cheshire-smile/CSULA_ECST_Claw_Machine/Design_Files/Alice - Claw_Machine_V3/7_3 Cube Parts/m5-hex-socket-screw/Renderings/M5x6.JPG

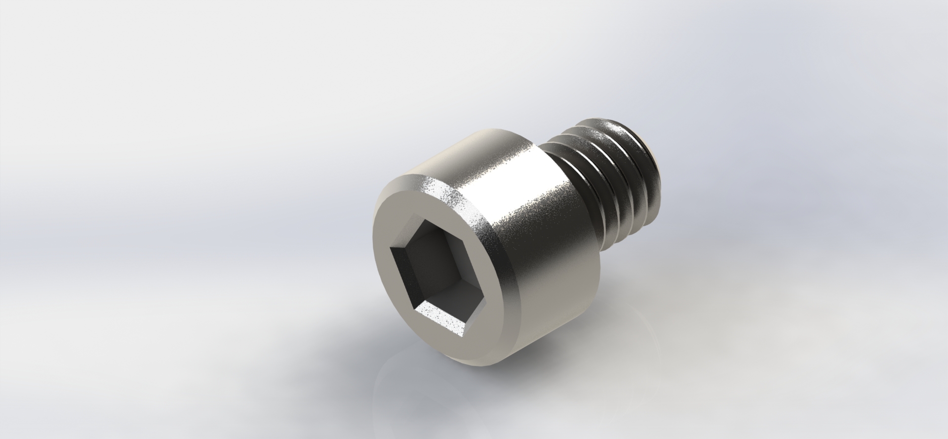
Design_Files/Alice - Claw_Machine_V3/7_3 Cube Parts/m5-hex-socket-screw/Renderings/M5x6.JPG
