cheshire-smile/CSULA_ECST_Claw_Machine/Design_Files/Alice - Claw_Machine_V3/7_3 Cube Parts/acyrlic/25.5inx22.44insideacyrlic.SLDPRT

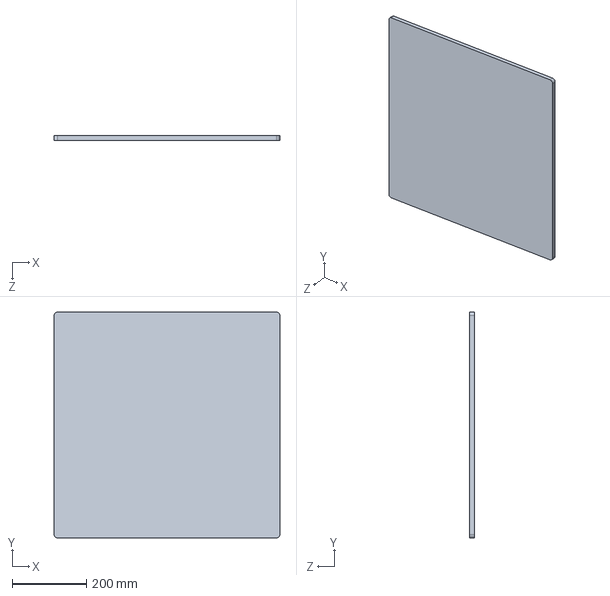
[picture p12: CAD file, 2025-05-13]
Design_Files/Alice - Claw_Machine_V3/7_3 Cube Parts/acyrlic/25.5inx22.44insideacyrlic.SLDPRT
609.6 x 609.6 x 12.7 mm
