cheshire-smile/CSULA_ECST_Claw_Machine/Design_Files/Alice - Claw_Machine_V3/7_3 Cube Parts/Sanwa JLF-TP-8YT  16Gate.step

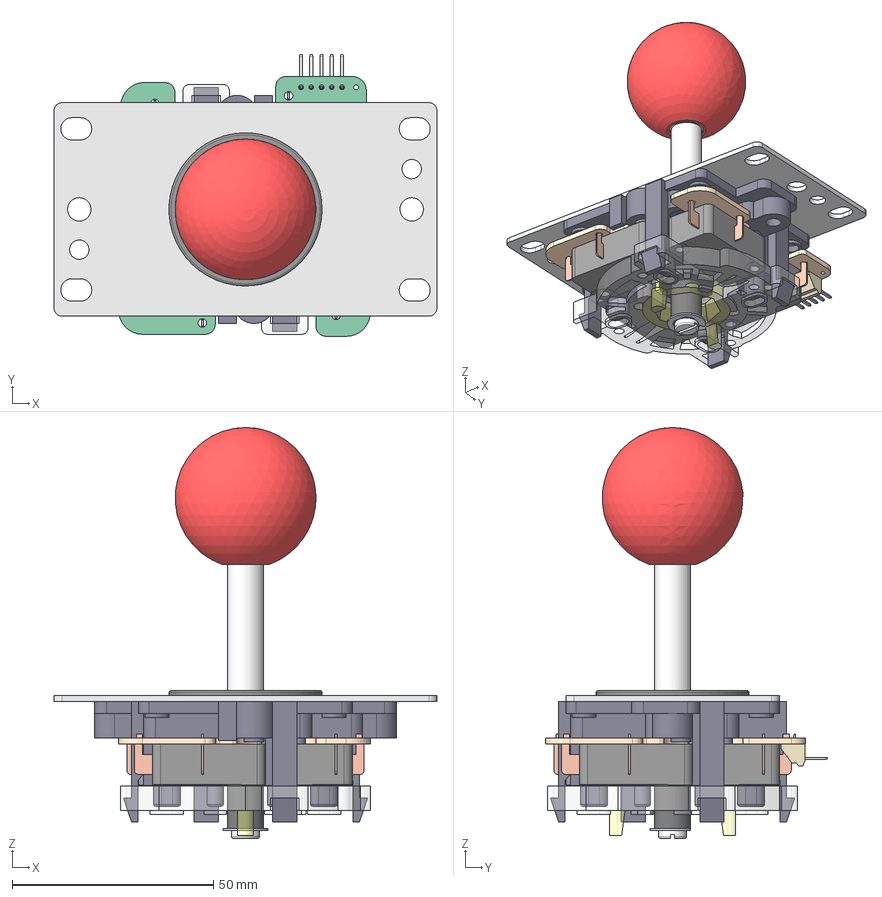
[picture p14: CAD file, 2025-05-13]
Design_Files/Alice - Claw_Machine_V3/7_3 Cube Parts/joystick and button/Sanwa JLF-TP-8YT 16Gate.step
95.0 x 69.9 x 102.0 mm
Connector 5P
JLF-P1 Mounting Plate
Sanwa LB-35 Balltop Dark Red
Sanwa JL-S9F Shaft
Solo Sanwa JLF Dustwasher
Sanwa LB-30 N-S Battop Adapter
Sanwa JLF P-2 Main Body
Sanwa JLF-P-4 Pivot
Push Button Arcade
Push Button Arcade_clne150
Push Button Arcade_clne151
Push Button Arcade_clne152
Sanwa JLF Actuator
Circlip
Sanwa JLF-P-6 Pressure Spring Base
Sanwa TP-MA PCB
Sanwa JLF-MW Washer
Sanwa JLF Spring
Sanwa GT-8F 16-Way Restrictor Plate
M3x10-Screw
M3x10-Screw001
M3x10-Screw002
M3x10-Screw003
M3-Nut
M3-Nut004
M3-Nut007
M3-Nut006
Sanwa GT Restrictor Plate
