cheshire-smile/CSULA_ECST_Claw_Machine/Design_Files/Alice - Claw_Machine_V3/7_3 Cube Parts/Microprocessor Cover.SLDPRT

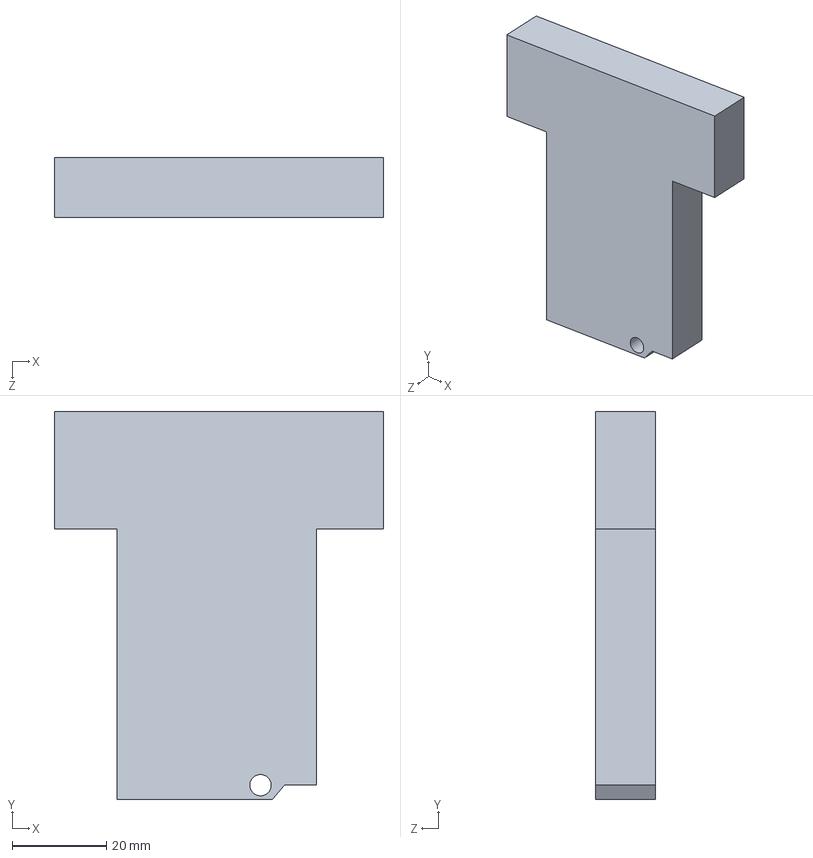
[picture p15: CAD file, 2025-05-13]
Design_Files/Alice - Claw_Machine_V3/7_3 Cube Parts/Microprocessor Cover.SLDPRT
70.0 x 82.5 x 12.7 mm
