cheshire-smile/CSULA_ECST_Claw_Machine/Design_Files/Alice - Claw_Machine_V3/7_3 Cube Parts/Sub_Assemblys/Corner_Idler_Pulley/Idler__Pulley/Bearing Seal, GT2 Timing Idler Pulley, Configurable.SLDPRT

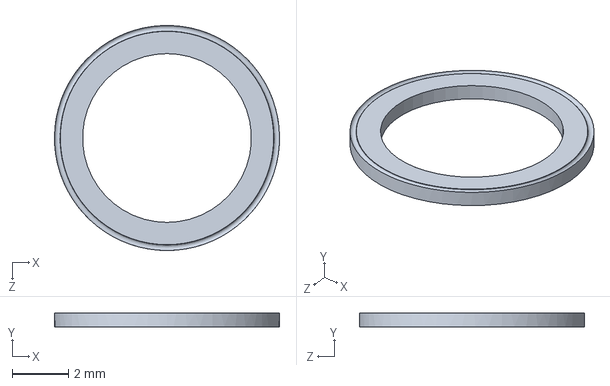
[picture p16: CAD file, 2025-05-13]
Design_Files/Alice - Claw_Machine_V3/7_3 Cube Parts/Sub_Assemblys/Corner_Idler_Pulley/Idler__Pulley/Bearing Seal, GT2 Timing Idler Pulley, Configurable.SLDPRT
8.00 x 0.5 x 8.00 mm
