cheshire-smile/CSULA_ECST_Claw_Machine/Design_Files/Alice - Claw_Machine_V3/7_3 Cube Parts/Sub_Assemblys/dc-micro-metal-gearmotor/Motor.stp

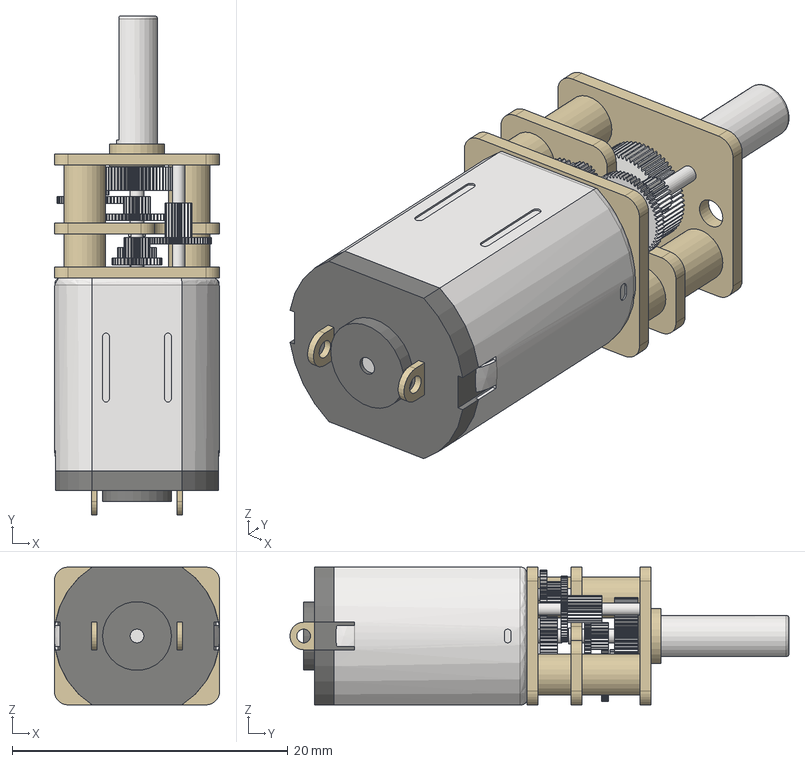
[picture p17: CAD file, 2025-05-13]
Design_Files/Alice - Claw_Machine_V3/7_3 Cube Parts/Sub_Assemblys/dc-micro-metal-gearmotor/Motor.stp
12.0 x 36.2 x 10.0 mm
Base
Rotor
Apoio Contato
Contato
Suporte Contato
Imãs
Terminais x 2
Escovas
Chapa Inferior
Chapa Intermediária
Chapa Superior
Eixo Maior - Engrenagem
Eixo Menor - Engrenagem
Parafuso x 2
Suporte Bobinas
Eixo Menor - Engrenagem_1
Engrenagem reta1
Engrenagem reta2
Engrenagem reta1_1
Engrenagem reta2_1
Eixo - Encaixe D
Engrenagem reta1_2
Engrenagem reta2_2
Engrenagem reta1_3
Engrenagem reta2_3
Engrenagem reta1_4
Engrenagem reta2_4
Carcaça
