cheshire-smile/CSULA_ECST_Claw_Machine/Design_Files/Alice - Claw_Machine_V3/7_3 Cube Parts/Sub_Assemblys/nema-17-stepper-motor/NEMA 17 Stepper Motor Shaft.SLDPRT

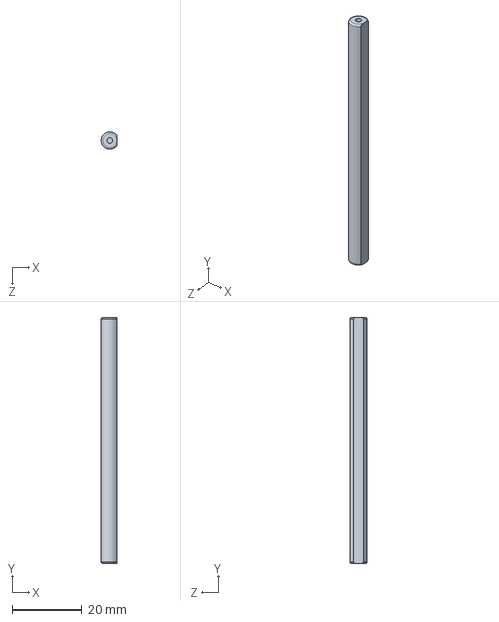
[picture p18: CAD file, 2025-05-13]
Design_Files/Alice - Claw_Machine_V3/7_3 Cube Parts/Sub_Assemblys/nema-17-stepper-motor/NEMA 17 Stepper Motor Shaft.SLDPRT
4.50 x 70.3 x 5.00 mm
