cheshire-smile/CSULA_ECST_Claw_Machine/Design_Files/Alice - Claw_Machine_V3/7_3 Cube Parts/Sub_Assemblys/V-Slot_Gantry_Plate/V-Slot Gantry Kit - 20mm.step

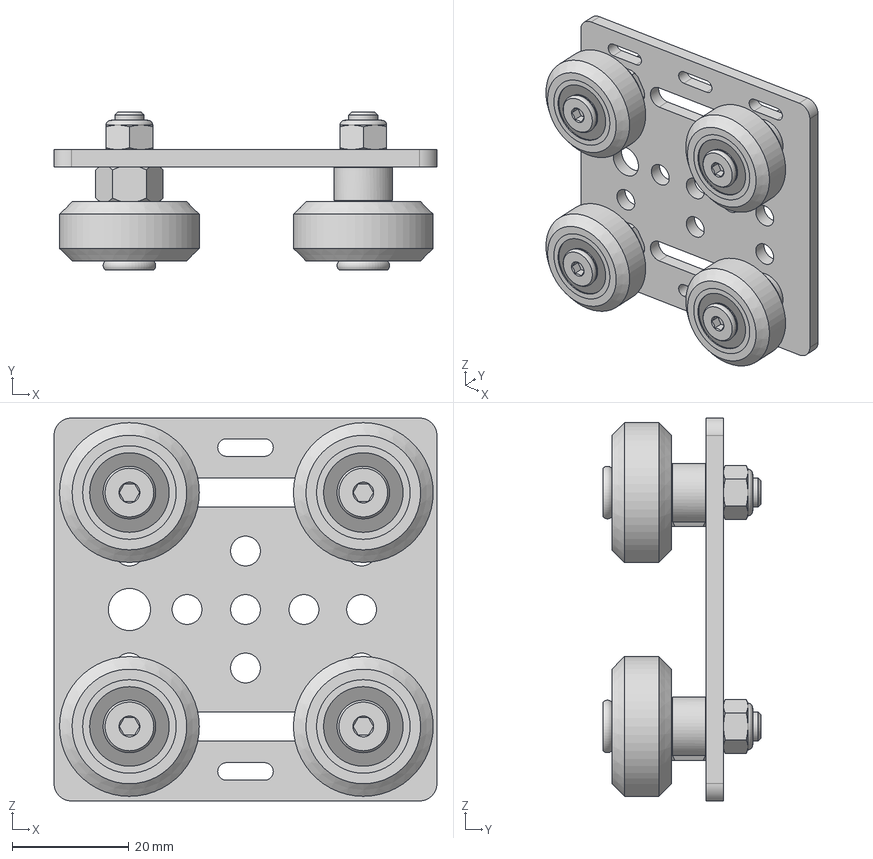
[picture p19: CAD file, 2025-05-13]
Design_Files/Alice - Claw_Machine_V3/7_3 Cube Parts/Sub_Assemblys/V-Slot_Gantry_Plate/V-Slot Gantry Kit - 20mm.step
65.5 x 27.0 x 65.5 mm
V-Slot Gantry Plate 20mm
Low Profile Screw M5 v1 x 4
Nylon Insert Lock Nut M5 x 4
Aluminum Spacer 6mm x 2
Eccentric Spacer 6mm v1 x 2
Ball Bearing 5 x 16 x 5 x 8
Precision Shim 8 x 5 x 1 x 4
Xtreme Solid V Wheel x 4
