cheshire-smile/CSULA_ECST_Claw_Machine/Design_Files/Alice - Claw_Machine_V3/7_3 Cube Parts/Winch/Updated Spool.SLDPRT

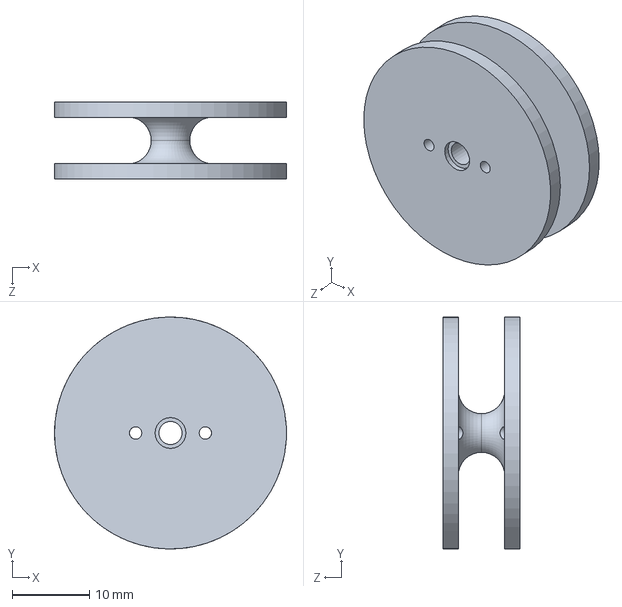
[picture p20: CAD file, 2025-05-13]
Design_Files/Alice - Claw_Machine_V3/7_3 Cube Parts/Winch/Updated Spool.SLDPRT
30.0 x 30.0 x 10.0 mm
