cheshire-smile/CSULA_ECST_Claw_Machine/Design_Files/Alice - Claw_Machine_V3/7_3 Cube Parts/wood/25.5inx13.57infrontbottomwoodhole.SLDPRT

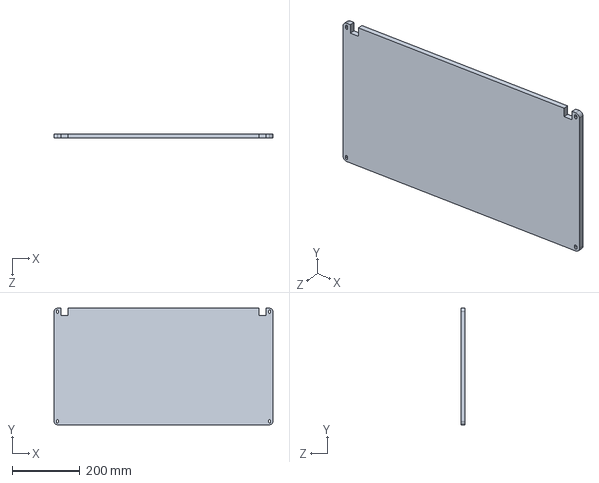
[picture p21: CAD file, 2025-05-13]
Design_Files/Alice - Claw_Machine_V3/7_3 Cube Parts/wood/25.5inx13.57infrontbottomwoodhole.SLDPRT
647.7 x 344.7 x 12.7 mm
