cheshire-smile/CSULA_ECST_Claw_Machine/Design_Files/Alice - Claw_Machine_V3/ST-M11.SLDPRT

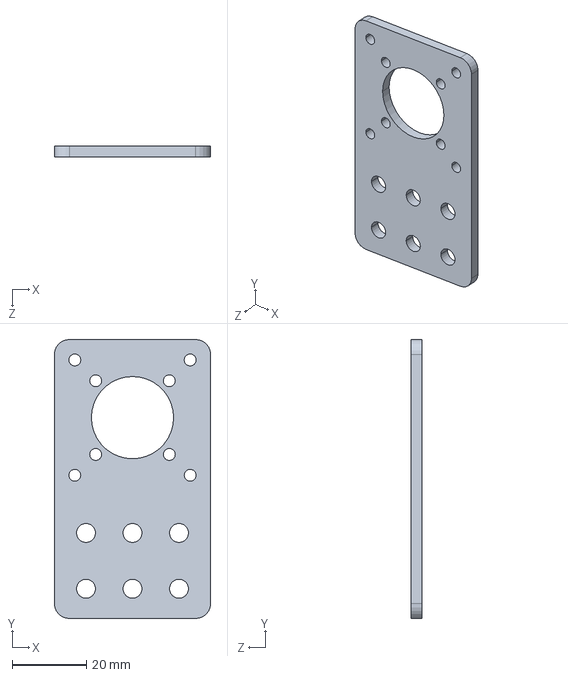
[picture p22: CAD file, 2025-05-13]
Design_Files/Alice - Claw_Machine_V3/ST-M11.SLDPRT
42.0 x 75.0 x 3.00 mm
