cheshire-smile/CSULA_ECST_Claw_Machine/Design_Files/Claw_Machine_V5/7_3 Cube Parts/acyrlic/25.5inx22.35infrontacyrlic.SLDPRT

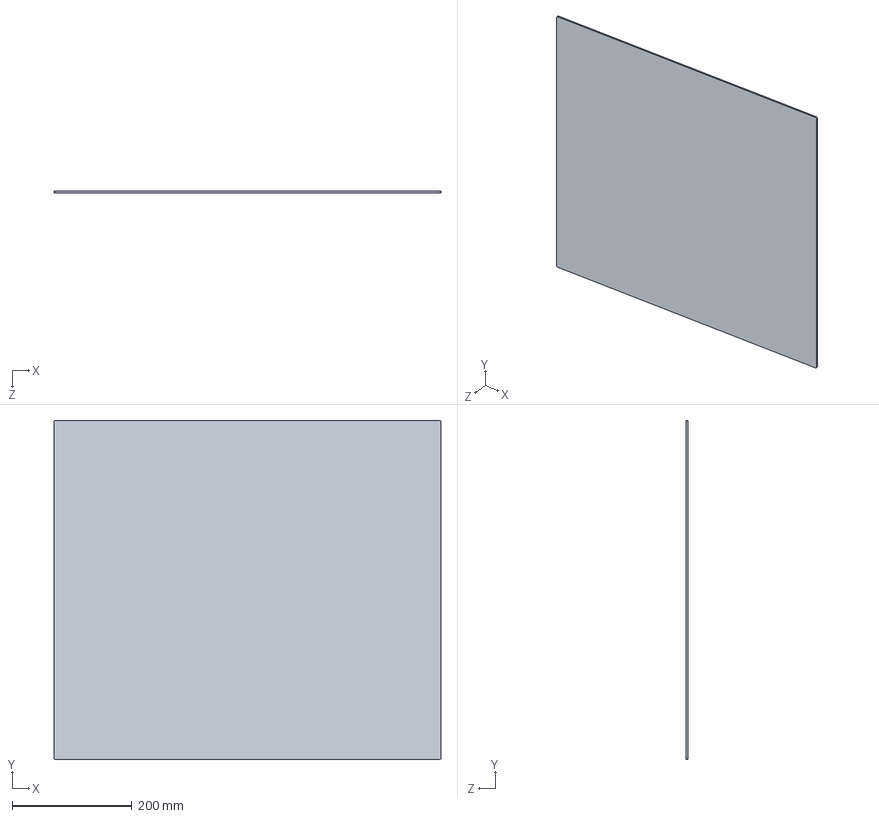
[picture p23: CAD file, 2025-09-01]
Design_Files/Claw_Machine_V5/7_3 Cube Parts/acyrlic/25.5inx22.35infrontacyrlic.SLDPRT
647.7 x 567.7 x 3.17 mm
