cheshire-smile/CSULA_ECST_Claw_Machine/Design_Files/Claw_Machine_V5/7_3 Cube Parts/aluminum_extrusion_2020/30inaluminum.SLDPRT

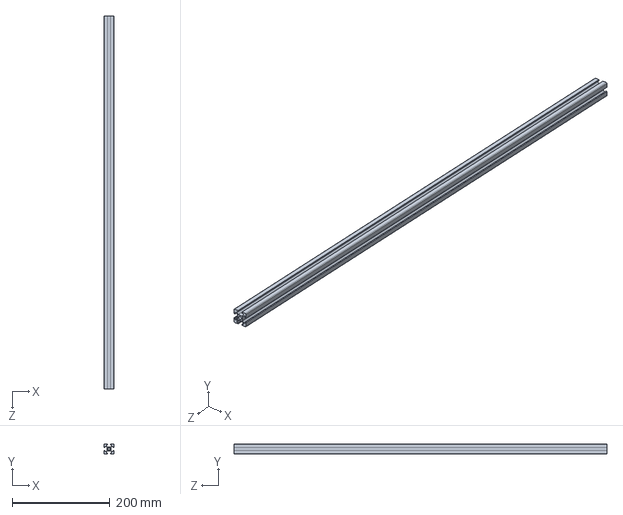
[picture p24: CAD file, 2025-09-01]
Design_Files/Claw_Machine_V5/7_3 Cube Parts/aluminum_extrusion_2020/30inaluminum.SLDPRT
20.0 x 20.0 x 762.0 mm
