cheshire-smile/CSULA_ECST_Claw_Machine/Design_Files/Claw_Machine_V5/7_3 Cube Parts/Sub_Assemblys/2020-extrusion-gt2-belt-tensioner/2020 Tensioner Long side.SLDPRT

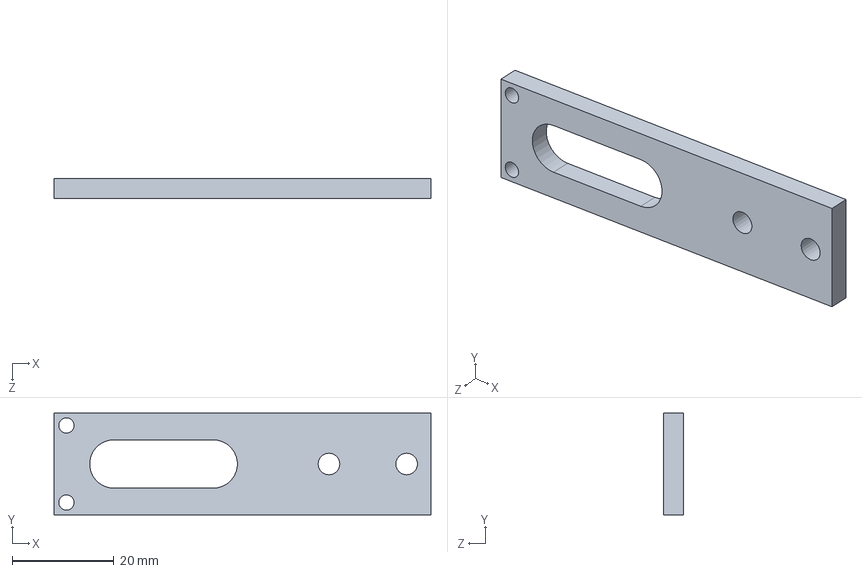
[picture p25: CAD file, 2025-09-01]
Design_Files/Claw_Machine_V5/7_3 Cube Parts/Sub_Assemblys/2020-extrusion-gt2-belt-tensioner/2020 Tensioner Long side.SLDPRT
74.0 x 20.0 x 4.00 mm
