cheshire-smile/CSULA_ECST_Claw_Machine/Design_Files/Claw_Machine_V5/7_3 Cube Parts/Sub_Assemblys/Corner_Idler_Pulley/Idler__Pulley/Bearing Ball, GT2 Timing Idler Pulley, Configurable.SLDPRT

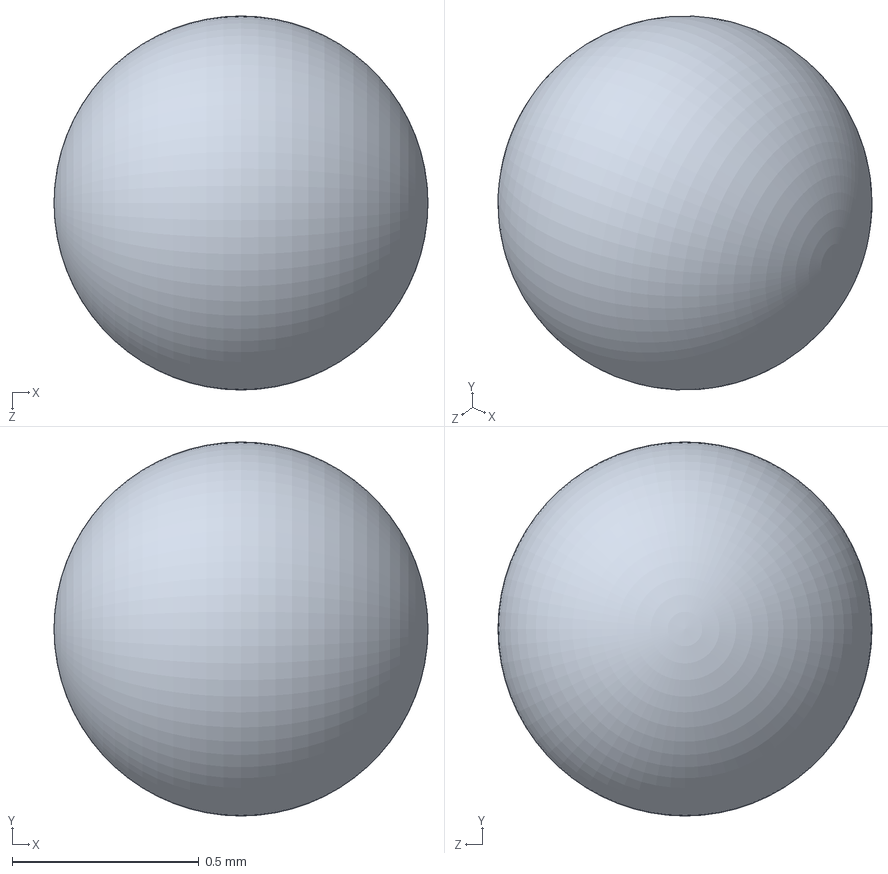
[picture p26: CAD file, 2025-09-01]
Design_Files/Claw_Machine_V5/7_3 Cube Parts/Sub_Assemblys/Corner_Idler_Pulley/Idler__Pulley/Bearing Ball, GT2 Timing Idler Pulley, Configurable.SLDPRT
1.00 x 1.00 x 1.00 mm
