cheshire-smile/CSULA_ECST_Claw_Machine/Design_Files/Claw_Machine_V5/7_3 Cube Parts/Sub_Assemblys/Winch/Gantry_Plate.SLDPRT

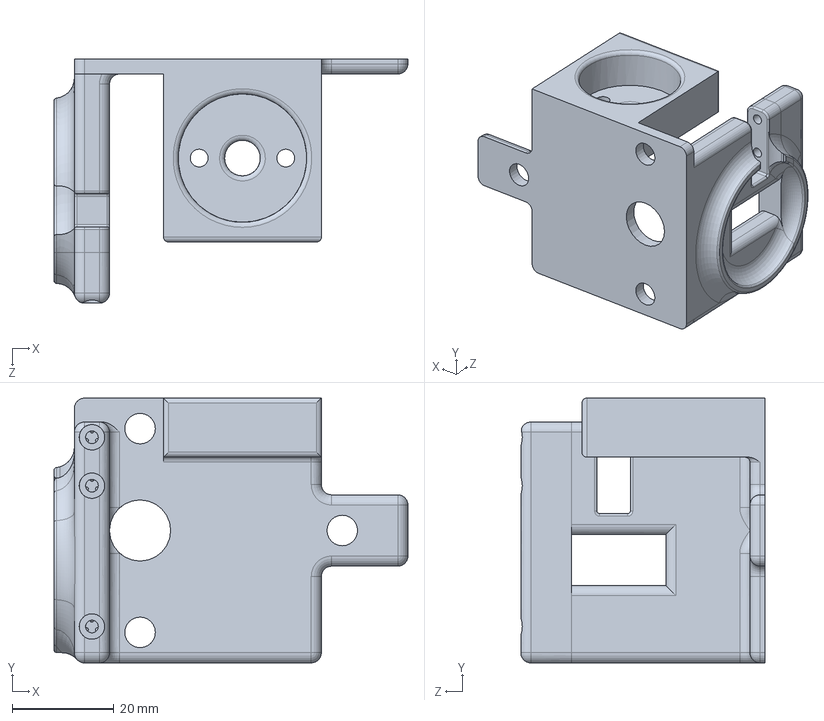
[picture p27: CAD file, 2025-09-02]
Design_Files/Claw_Machine_V5/7_3 Cube Parts/Sub_Assemblys/Winch/Gantry_Plate.SLDPRT
69.5 x 52.0 x 48.0 mm
