cheshire-smile/CSULA_ECST_Claw_Machine/Design_Files/Claw_Machine_V5/7_3 Cube Parts/wood/23.92inx4.43infrontwoodforjoystick.SLDPRT

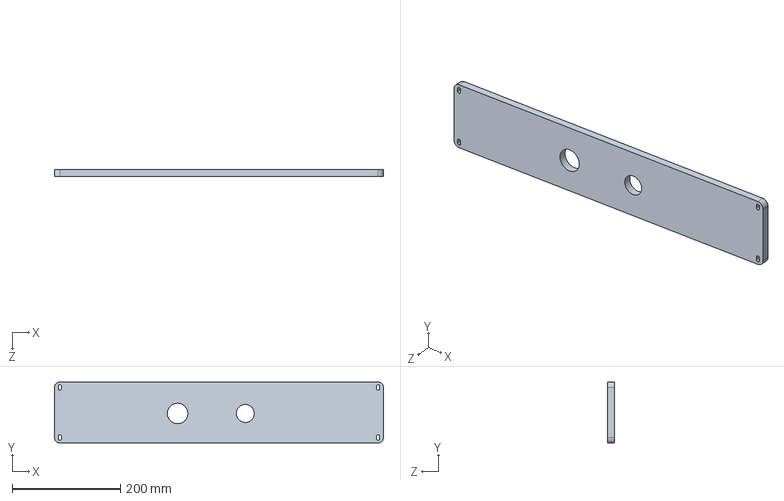
[picture p28: CAD file, 2025-09-01]
Design_Files/Claw_Machine_V5/7_3 Cube Parts/wood/23.92inx4.43infrontwoodforjoystick.SLDPRT
607.6 x 112.5 x 12.7 mm
