cheshire-smile/CSULA_ECST_Claw_Machine/Design_Files/Claw_Machine_V5/7_3 Cube Parts/X-Axis_Mounting_Bracket.SLDPRT

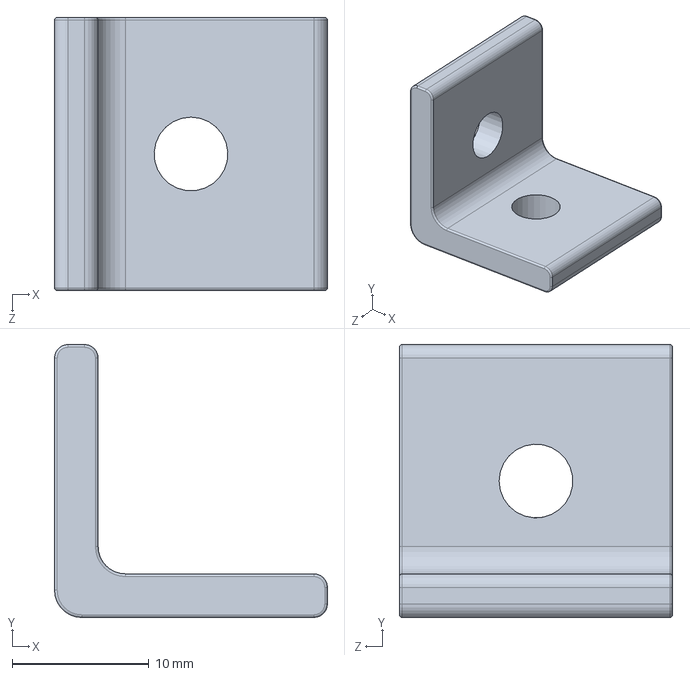
[picture p29: CAD file, 2025-09-01]
Design_Files/Claw_Machine_V5/7_3 Cube Parts/X-Axis_Mounting_Bracket.SLDPRT
20.0 x 20.0 x 20.0 mm
