cheshire-smile/CSULA_ECST_Claw_Machine/Design_Files/Alice - Claw_Machine_V3/7_3 Cube Parts/aluminum_extrusion_2020/36inaluminum.SLDPRT

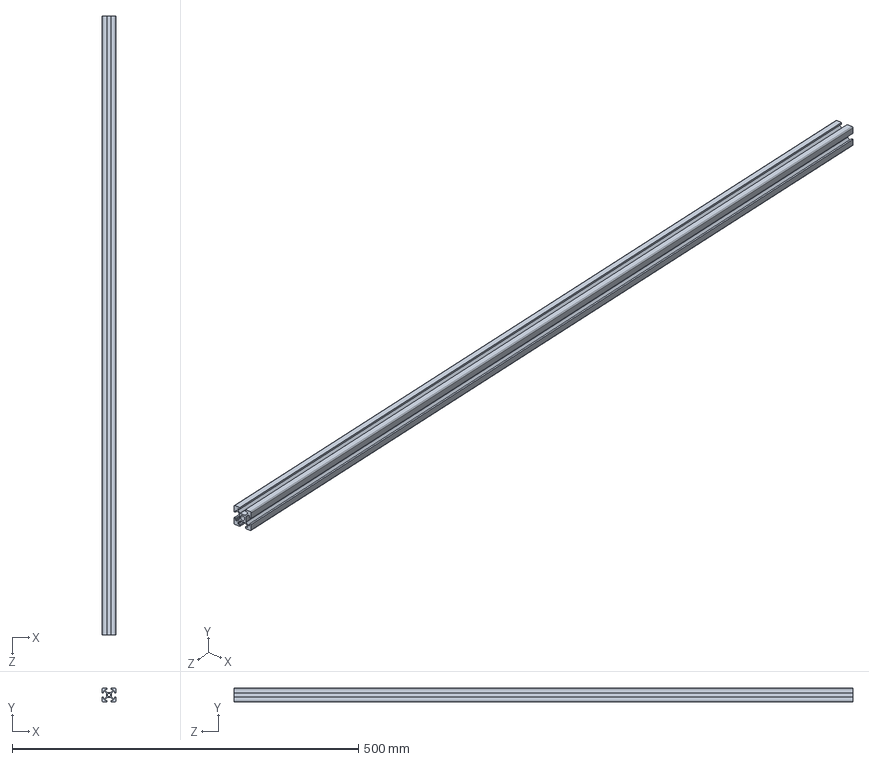
[picture p30: CAD file, 2025-05-13]
Design_Files/Alice - Claw_Machine_V3/7_3 Cube Parts/aluminum_extrusion_2020/36inaluminum.SLDPRT
20.0 x 20.0 x 894.4 mm
