cheshire-smile/CSULA_ECST_Claw_Machine/Design_Files/Alice - Claw_Machine_V3/7_3 Cube Parts/joystick and button/Adafruit 30mm Button with LED v2.step

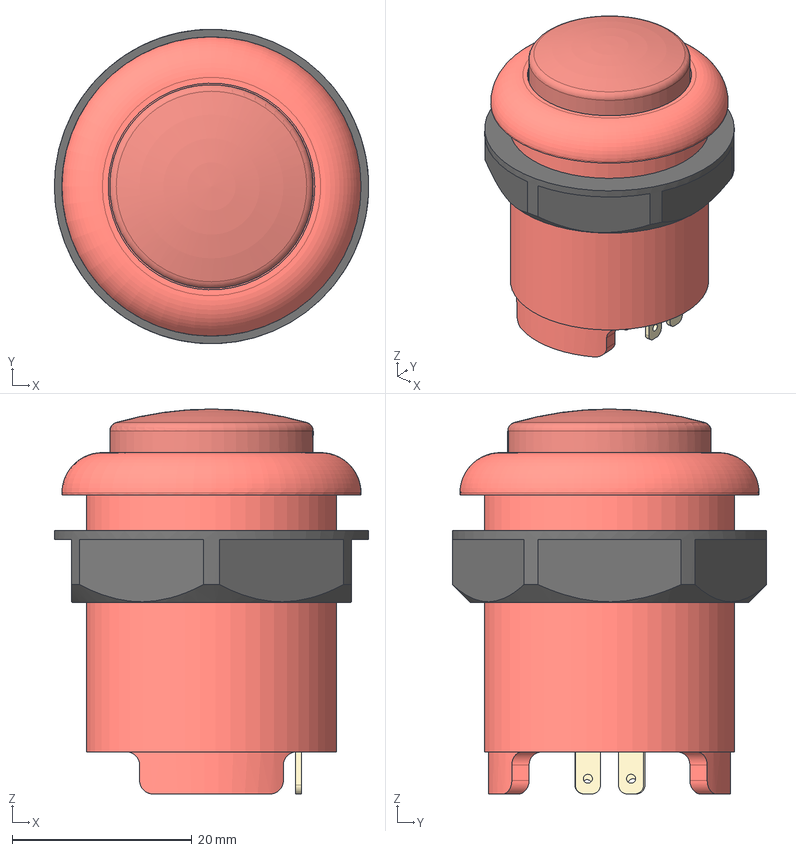
[picture p31: CAD file, 2025-05-13]
Design_Files/Alice - Claw_Machine_V3/7_3 Cube Parts/joystick and button/Adafruit 30mm Button with LED v2.step
35.0 x 35.0 x 42.9 mm
shell_body
nut
button_body
pins
led_pins
