cheshire-smile/CSULA_ECST_Claw_Machine/Design_Files/Alice - Claw_Machine_V3/7_3 Cube Parts/Pulley_GT2_20T_b5.SLDPRT

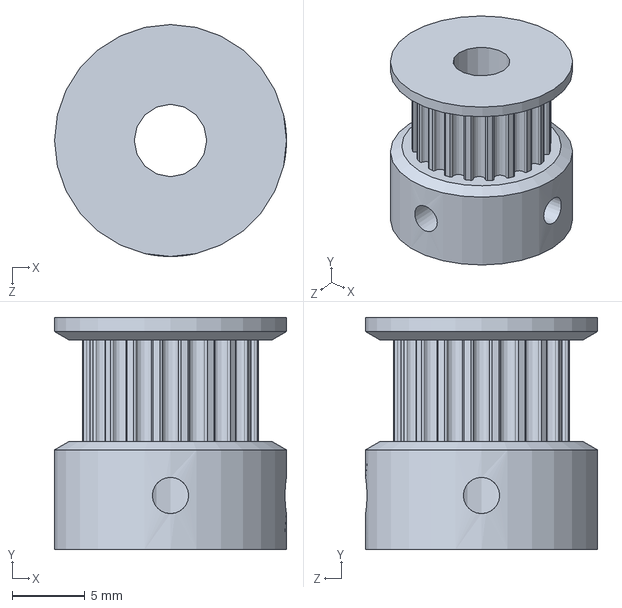
[picture p32: CAD file, 2025-05-13]
Design_Files/Alice - Claw_Machine_V3/7_3 Cube Parts/Pulley_GT2_20T_b5.SLDPRT
16.0 x 16.0 x 16.0 mm
