cheshire-smile/CSULA_ECST_Claw_Machine/Design_Files/Alice - Claw_Machine_V3/7_3 Cube Parts/Sub_Assemblys/2020-extrusion-gt2-belt-tensioner/2020 Belt Tensioner G_K.STEP

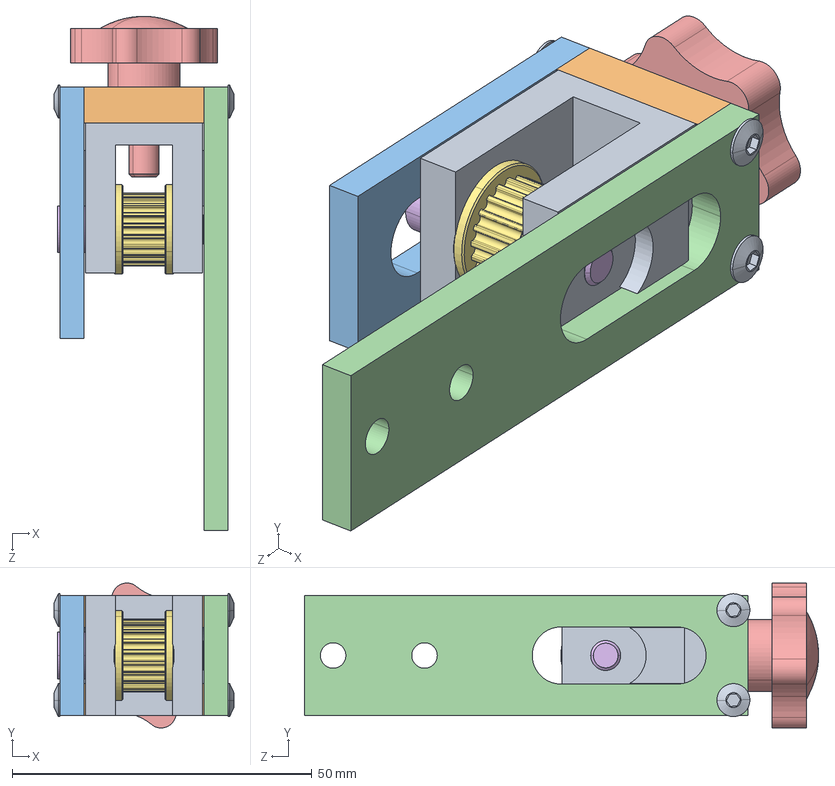
[picture p33: CAD file, 2025-05-13]
Design_Files/Alice - Claw_Machine_V3/7_3 Cube Parts/Sub_Assemblys/2020-extrusion-gt2-belt-tensioner/2020 Belt Tensioner G_K.STEP
30.0 x 24.2 x 85.8 mm
2020 Tensioner Pulley Cradle
2020 Tensioner Rear
2020 Tensioner Short side
2020 Tensioner Long side
2020 Tensioner Adjusting Screw
M5 Cap head Screw
GT2_Idler_20T.step
Ball bearing (5x9x3)mm003.step
Ball bearing (5x9x3)mm004.step
M3x10mm bolt x 4
