cheshire-smile/CSULA_ECST_Claw_Machine/Design_Files/Alice - Claw_Machine_V3/7_3 Cube Parts/Sub_Assemblys/Corner_Idler_Pulley/Idler__Pulley/Bearing Inner Ring, GT2 Timing Idler Pulley, Configurable.SLDPRT

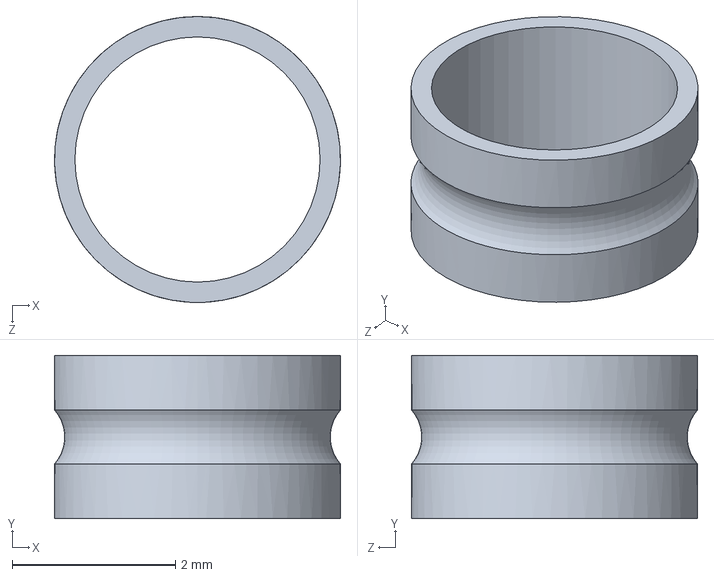
[picture p34: CAD file, 2025-05-13]
Design_Files/Alice - Claw_Machine_V3/7_3 Cube Parts/Sub_Assemblys/Corner_Idler_Pulley/Idler__Pulley/Bearing Inner Ring, GT2 Timing Idler Pulley, Configurable.SLDPRT
3.50 x 2.00 x 3.50 mm
