cheshire-smile/CSULA_ECST_Claw_Machine/Design_Files/Alice - Claw_Machine_V3/7_3 Cube Parts/Sub_Assemblys/nema-17-stepper-motor/NEMA 17 Stepper Motor SIMPLE.IGS

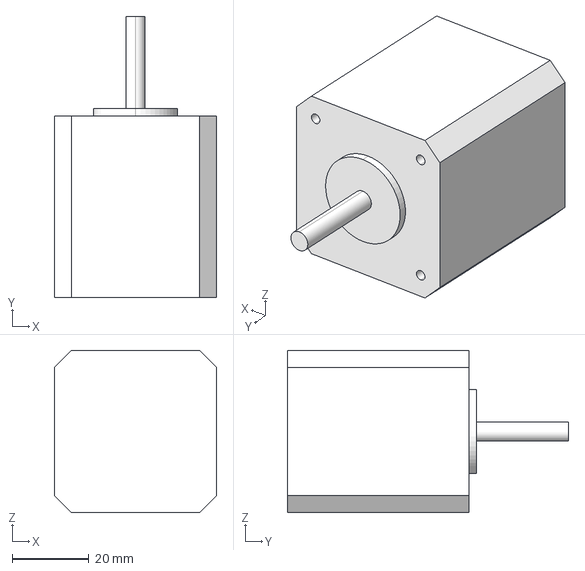
[picture p35: CAD file, 2025-05-13]
Design_Files/Alice - Claw_Machine_V3/7_3 Cube Parts/Sub_Assemblys/nema-17-stepper-motor/NEMA 17 Stepper Motor SIMPLE.IGS
42.3 x 73.3 x 42.3 mm
