cheshire-smile/CSULA_ECST_Claw_Machine/Design_Files/Alice - Claw_Machine_V3/7_3 Cube Parts/Winch/Outer part 26mm.SLDPRT

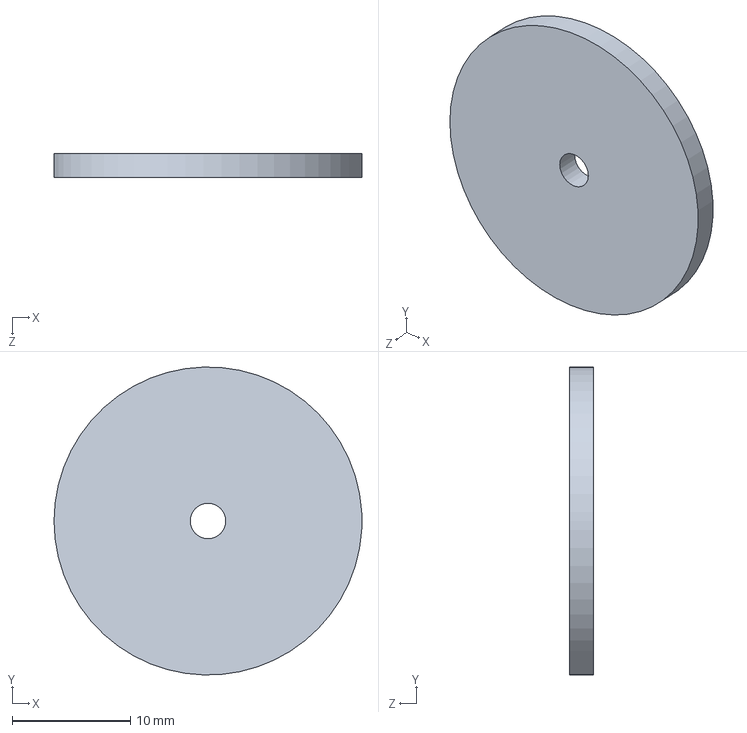
[picture p36: CAD file, 2025-05-13]
Design_Files/Alice - Claw_Machine_V3/7_3 Cube Parts/Winch/Outer part 26mm.SLDPRT
26.0 x 26.0 x 2.00 mm
