cheshire-smile/CSULA_ECST_Claw_Machine/Design_Files/Claw_Machine_V5/7_3 Cube Parts/acyrlic/25.5inx22.44insideacyrlic.SLDPRT

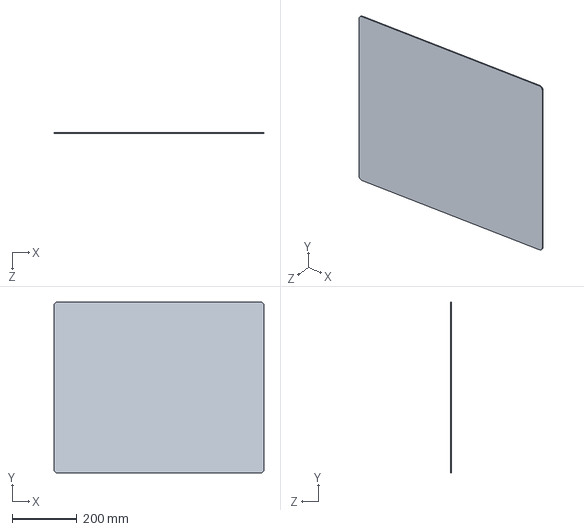
[picture p37: CAD file, 2025-09-01]
Design_Files/Claw_Machine_V5/7_3 Cube Parts/acyrlic/25.5inx22.44insideacyrlic.SLDPRT
647.7 x 527.0 x 3.17 mm
