cheshire-smile/CSULA_ECST_Claw_Machine/Design_Files/Claw_Machine_V5/7_3 Cube Parts/Sub_Assemblys/Mini Servo operated Claw Machine Claw Grabber - 4826548/files/Claw_cover.SLDPRT

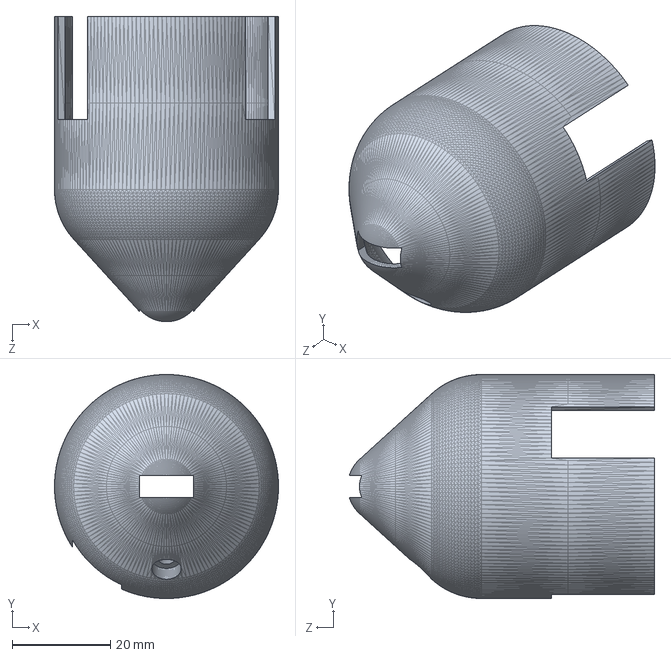
[picture p40: CAD file, 2025-09-01]
Design_Files/Claw_Machine_V5/7_3 Cube Parts/Sub_Assemblys/Mini Servo operated Claw Machine Claw Grabber - 4826548/files/Claw_cover.SLDPRT
45.5 x 45.5 x 62.0 mm
