cheshire-smile/CSULA_ECST_Claw_Machine/Design_Files/Claw_Machine_V5/7_3 Cube Parts/Sub_Assemblys/nema-17-stepper-motor/NEMA 17 Stepper Motor Top.SLDPRT

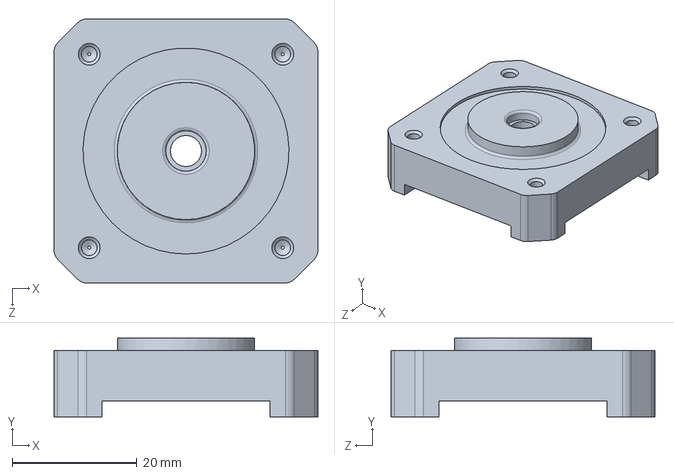
[picture p41: CAD file, 2025-09-01]
Design_Files/Claw_Machine_V5/7_3 Cube Parts/Sub_Assemblys/nema-17-stepper-motor/NEMA 17 Stepper Motor Top.SLDPRT
42.3 x 12.6 x 42.3 mm
