cheshire-smile/CSULA_ECST_Claw_Machine/Design_Files/Claw_Machine_V5/7_3 Cube Parts/Sub_Assemblys/Winch/Crane_Spool_forCNC.SLDPRT

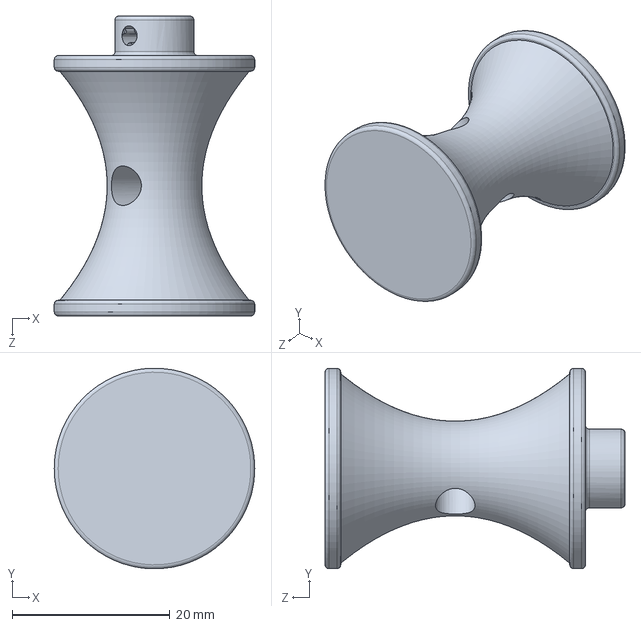
[picture p42: CAD file, 2025-09-02]
Design_Files/Claw_Machine_V5/7_3 Cube Parts/Sub_Assemblys/Winch/Crane_Spool_forCNC.SLDPRT
25.4 x 25.4 x 38.0 mm
