cheshire-smile/CSULA_ECST_Claw_Machine/Design_Files/Alice - Claw_Machine_V3/7_3 Cube Parts/wood/24.08inx23.92ininsidewood.SLDPRT

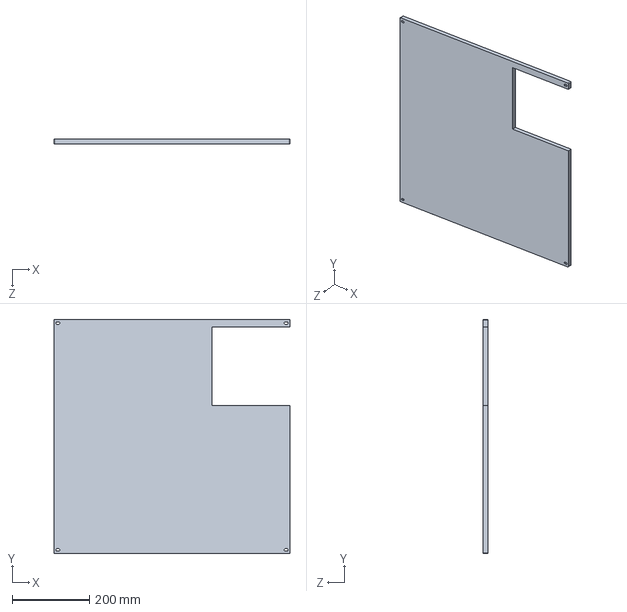
[picture p43: CAD file, 2025-05-13]
Design_Files/Alice - Claw_Machine_V3/7_3 Cube Parts/wood/24.08inx23.92ininsidewood.SLDPRT
611.6 x 607.6 x 12.7 mm
