cheshire-smile/CSULA_ECST_Claw_Machine/Design_Files/Claw_Machine_V5/7_3 Cube Parts/acyrlic/25.5inx22.35infrontacyrlic87.DXF

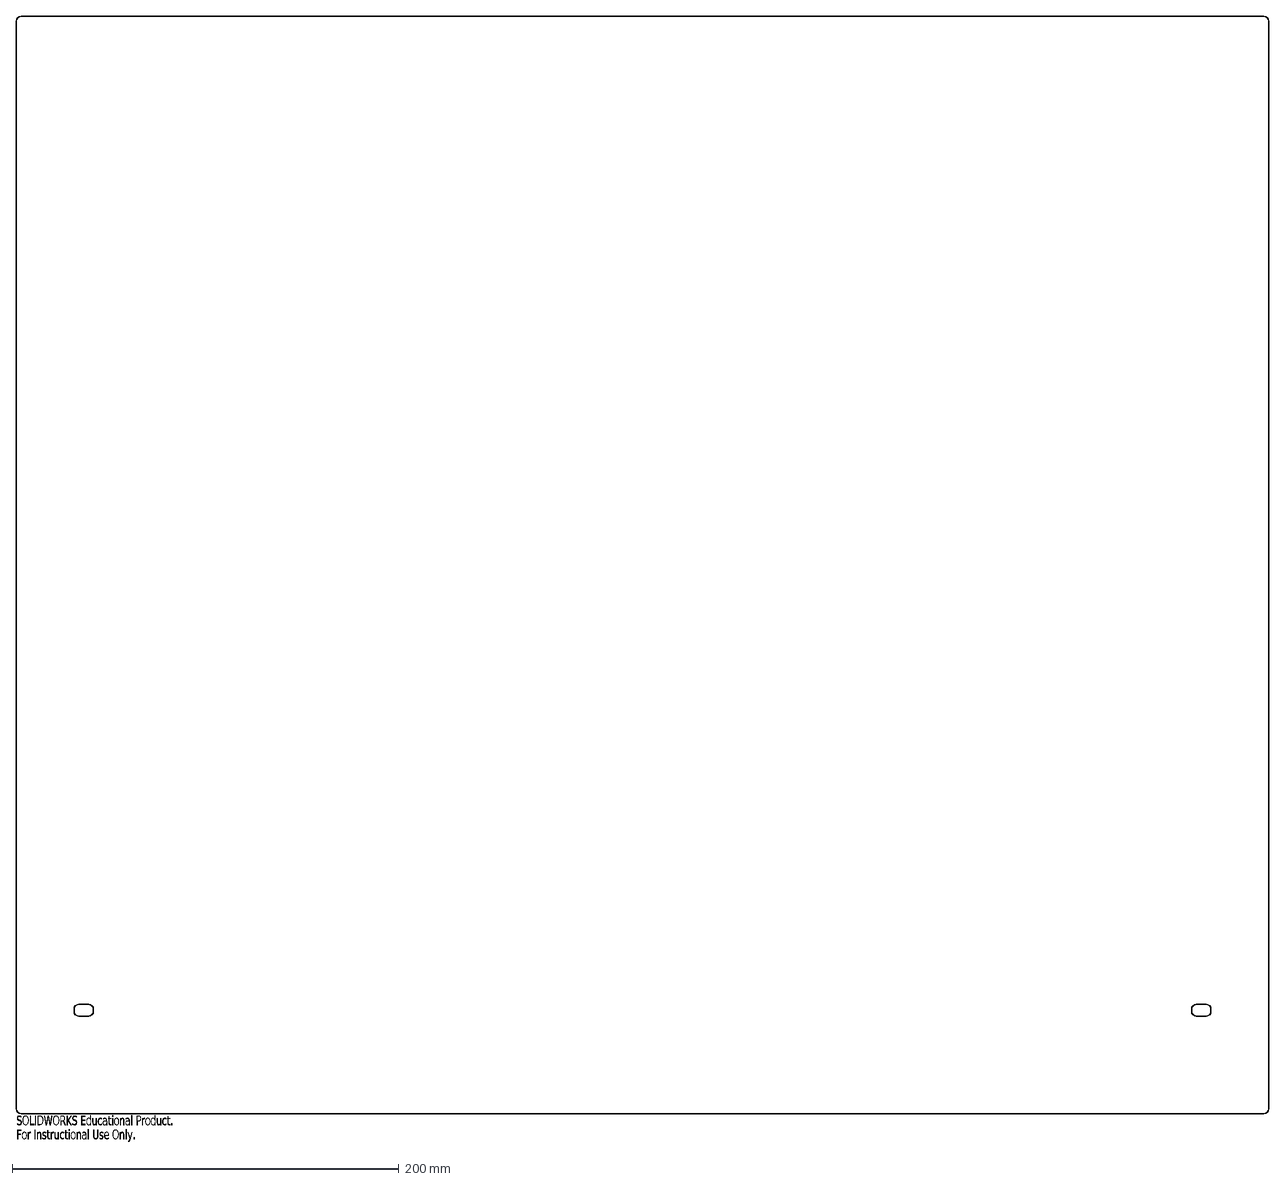
[picture p44: CAD file, 2025-05-13]
Design_Files/Claw_Machine_V5/7_3 Cube Parts/acyrlic/25.5inx22.35infrontacyrlic87.DXF
SOLIDWORKS Educational Product.
For Instructional Use Only.
