cheshire-smile/CSULA_ECST_Claw_Machine/Design_Files/Claw_Machine_V5/7_3 Cube Parts/Corner_Idler_Pulley.SLDPRT

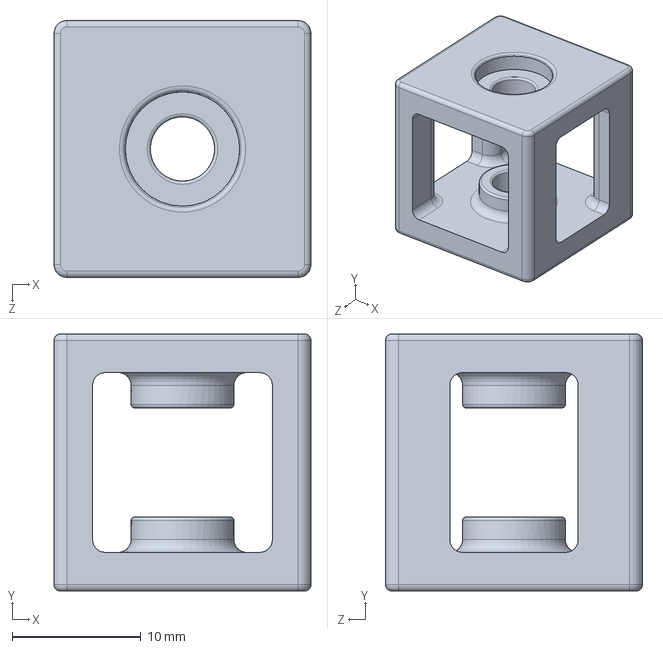
[picture p45: CAD file, 2025-09-01]
Design_Files/Claw_Machine_V5/7_3 Cube Parts/Corner_Idler_Pulley.SLDPRT
20.0 x 20.0 x 20.0 mm
