cheshire-smile/CSULA_ECST_Claw_Machine/Design_Files/Claw_Machine_V5/7_3 Cube Parts/Sub_Assemblys/Mini Servo operated Claw Machine Claw Grabber - 4826548/files/Driven_Arm.SLDPRT

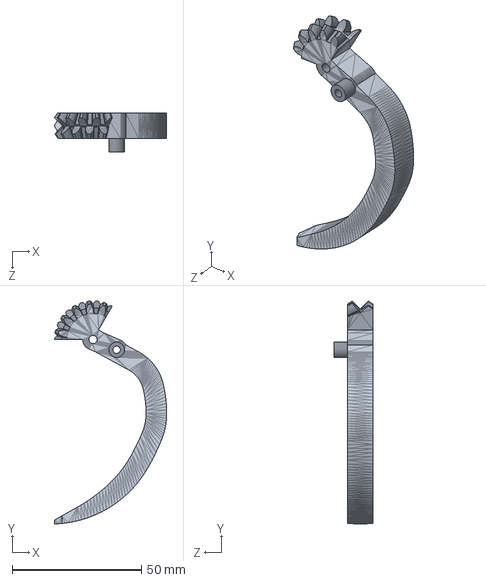
[picture p46: CAD file, 2025-09-01]
Design_Files/Claw_Machine_V5/7_3 Cube Parts/Sub_Assemblys/Mini Servo operated Claw Machine Claw Grabber - 4826548/files/Driven_Arm.SLDPRT
43.6 x 86.4 x 15.2 mm
