cheshire-smile/CSULA_ECST_Claw_Machine/Design_Files/Claw_Machine_V5/7_3 Cube Parts/wood/25.5inx13.52incutsidebottomwood.SLDPRT

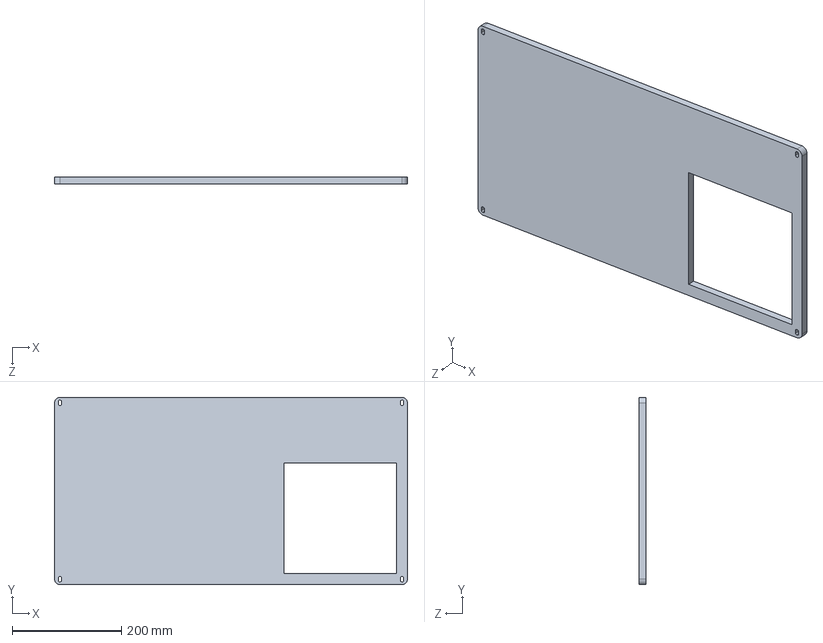
[picture p48: CAD file, 2025-09-01]
Design_Files/Claw_Machine_V5/7_3 Cube Parts/wood/25.5inx13.52incutsidebottomwood.SLDPRT
647.7 x 343.4 x 12.7 mm
