cheshire-smile/CSULA_ECST_Claw_Machine/Design_Files/Claw_Machine_V5/NO-NC Bump Switch.step

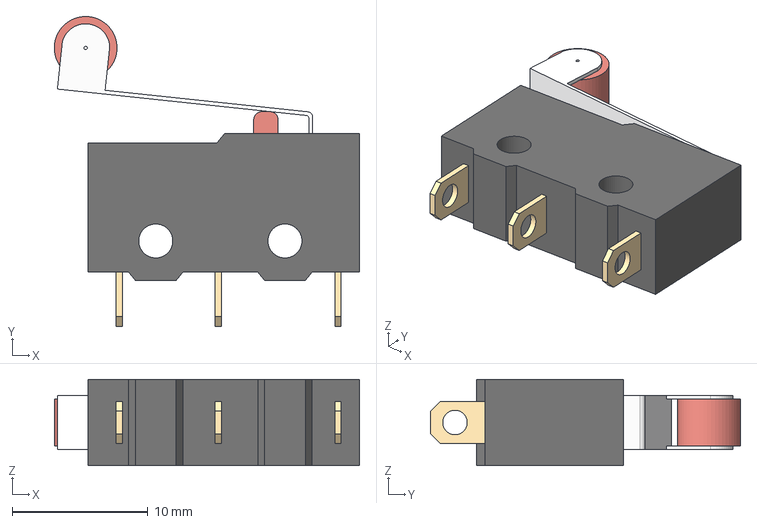
[picture p49: CAD file, 2025-05-16]
Design_Files/Claw_Machine_V5/NO-NC Bump Switch.step
22.5 x 22.8 x 6.34 mm
