cheshire-smile/CSULA_ECST_Claw_Machine/Design_Files/updated front acyrlic.SLDPRT

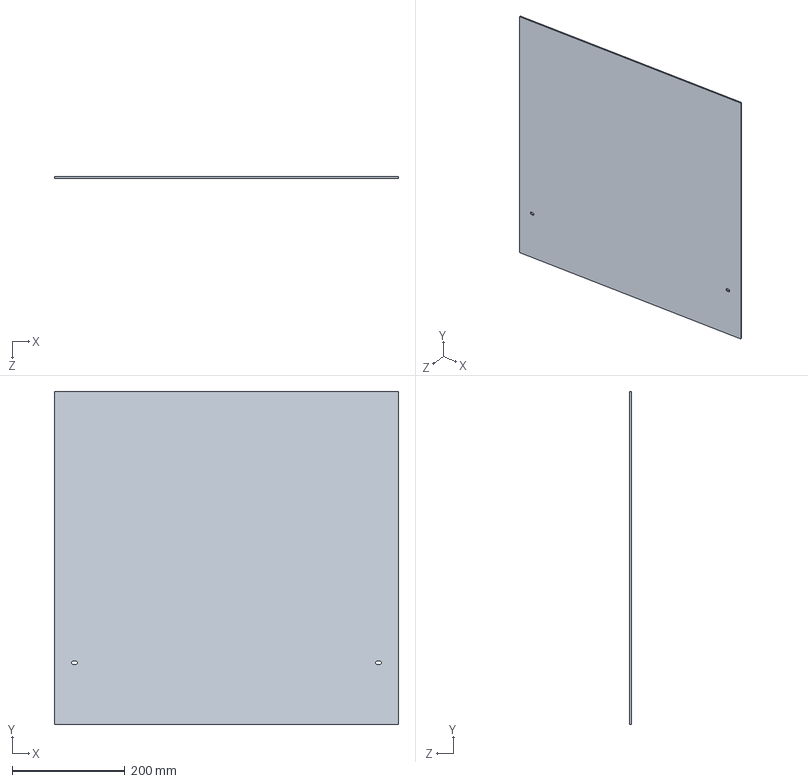
[picture p50: CAD file, 2025-05-13]
Design_Files/updated front acyrlic.SLDPRT
609.6 x 590.5 x 3.17 mm
