cheshire-smile/CSULA_ECST_Claw_Machine/Design_Files/Alice - Claw_Machine_V3/7_3 Cube Parts/Sub_Assemblys/2020-extrusion-gt2-belt-tensioner/2020 Tensioner Pulley Cradle.SLDPRT

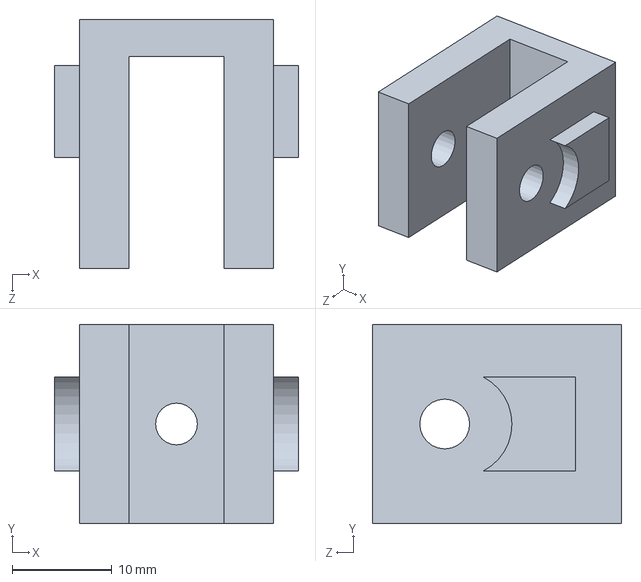
[picture p51: CAD file, 2025-05-13]
Design_Files/Alice - Claw_Machine_V3/7_3 Cube Parts/Sub_Assemblys/2020-extrusion-gt2-belt-tensioner/2020 Tensioner Pulley Cradle.SLDPRT
24.5 x 20.0 x 25.0 mm
