cheshire-smile/CSULA_ECST_Claw_Machine/Design_Files/Alice - Claw_Machine_V3/7_3 Cube Parts/wood/23.92inx6infrontwoodforjoystick.SLDPRT

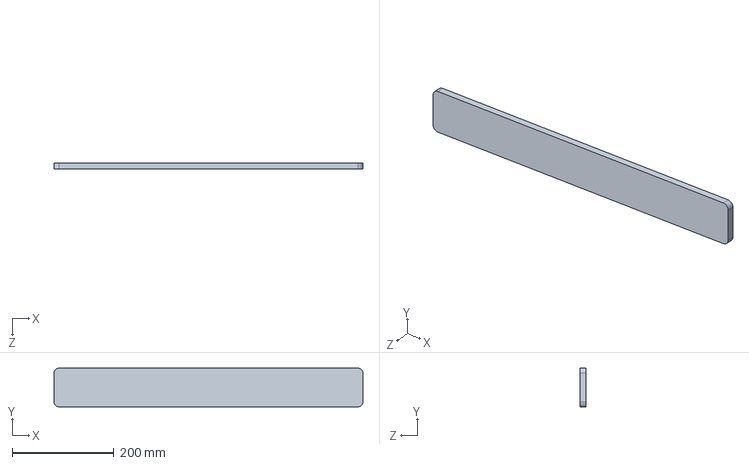
[picture p52: CAD file, 2025-05-13]
Design_Files/Alice - Claw_Machine_V3/7_3 Cube Parts/wood/23.92inx6infrontwoodforjoystick.SLDPRT
607.6 x 76.2 x 12.7 mm
