cheshire-smile/CSULA_ECST_Claw_Machine/Design_Files/Claw_Machine_V5/7_3 Cube Parts/Sub_Assemblys/Corner_Idler_Pulley/Idler__Pulley/Body, GT2 Timing Idler Pulley, Configurable.SLDPRT

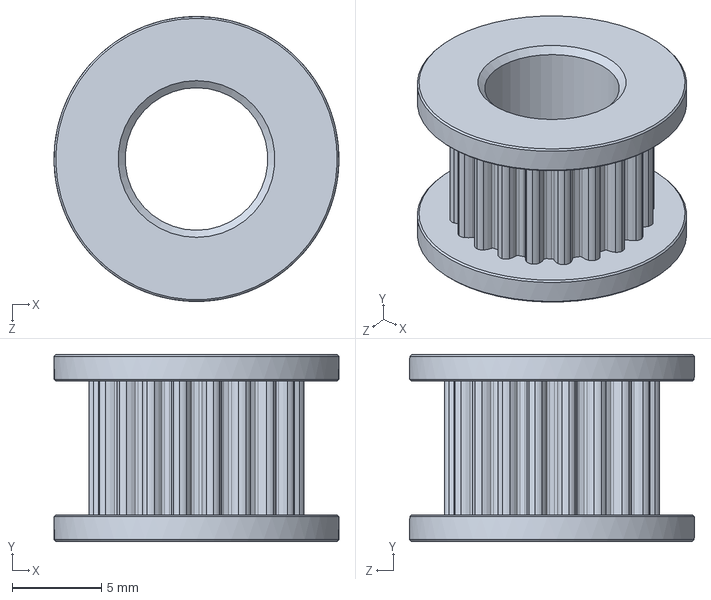
[picture p53: CAD file, 2025-09-01]
Design_Files/Claw_Machine_V5/7_3 Cube Parts/Sub_Assemblys/Corner_Idler_Pulley/Idler__Pulley/Body, GT2 Timing Idler Pulley, Configurable.SLDPRT
16.0 x 10.5 x 16.0 mm
