cheshire-smile/CSULA_ECST_Claw_Machine/Design_Files/Claw_Machine_V5/7_3 Cube Parts/Sub_Assemblys/Mini Servo operated Claw Machine Claw Grabber - 4826548/files/Servo_Linkage_Part_1.SLDPRT

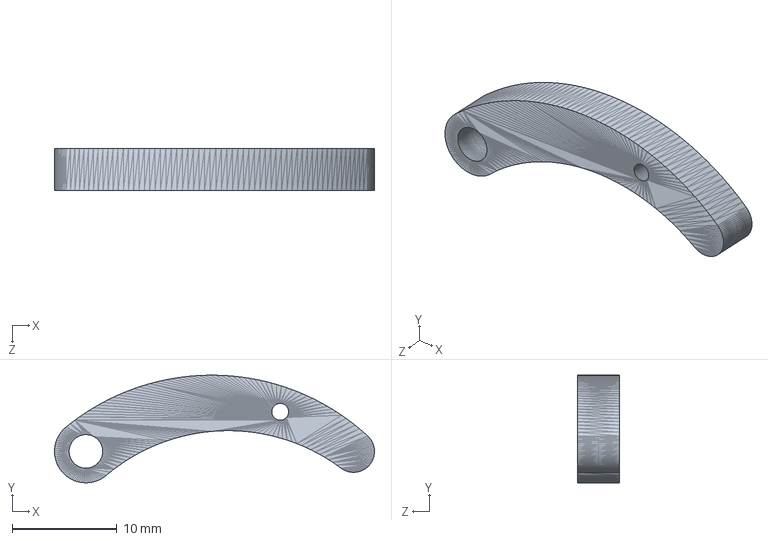
[picture p54: CAD file, 2025-05-13]
Design_Files/Claw_Machine_V5/7_3 Cube Parts/Sub_Assemblys/Mini Servo operated Claw Machine Claw Grabber - 4826548/files/Servo_Linkage_Part_1.SLDPRT
30.5 x 10.3 x 4.00 mm
