cheshire-smile/CSULA_ECST_Claw_Machine/Design_Files/Claw_Machine_V5/7_3 Cube Parts/Sub_Assemblys/Winch/25d-metal-gearmotor-34-47.step

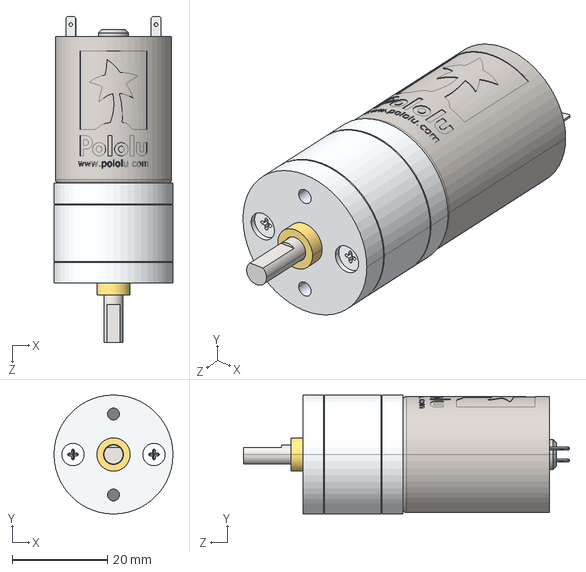
[picture p56: CAD file, 2025-09-01]
Design_Files/Claw_Machine_V5/7_3 Cube Parts/Sub_Assemblys/Winch/25d-metal-gearmotor-34-47.step
25.0 x 25.0 x 68.5 mm
