cheshire-smile/CSULA_ECST_Claw_Machine/Design_Files/Alice - Claw_Machine_V3/7_3 Cube Parts/Winch/Connecting Piece.SLDPRT

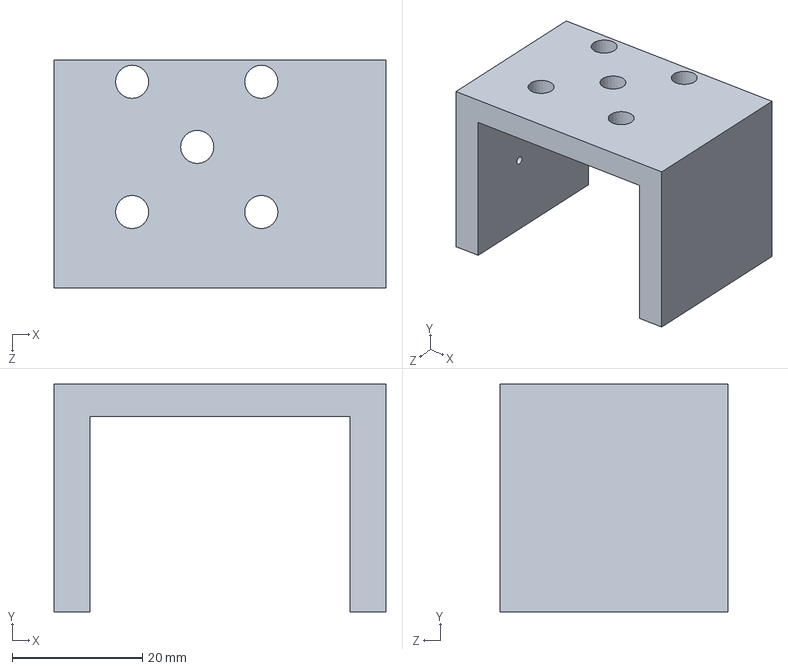
[picture p57: CAD file, 2025-05-13]
Design_Files/Alice - Claw_Machine_V3/7_3 Cube Parts/Winch/Connecting Piece.SLDPRT
51.0 x 35.0 x 35.0 mm
