cheshire-smile/CSULA_ECST_Claw_Machine/Design_Files/Claw_Machine_V5/7_3 Cube Parts/Sub_Assemblys/Mini Servo operated Claw Machine Claw Grabber - 4826548/files/Non-Driven_Arm.SLDPRT

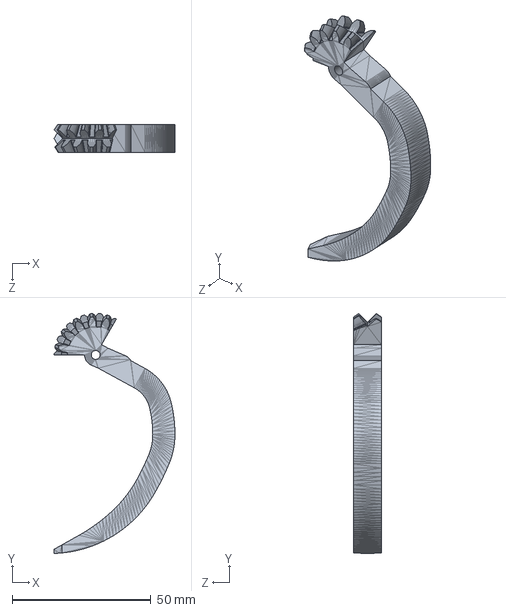
[picture p60: CAD file, 2025-05-13]
Design_Files/Claw_Machine_V5/7_3 Cube Parts/Sub_Assemblys/Mini Servo operated Claw Machine Claw Grabber - 4826548/files/Non-Driven_Arm.SLDPRT
43.6 x 86.4 x 10.0 mm
