cheshire-smile/CSULA_ECST_Claw_Machine/Design_Files/Alice - Claw_Machine_V3/7_3 Cube Parts/Sub_Assemblys/2020-extrusion-gt2-belt-tensioner/GT2_Idler_20T_6mm.step

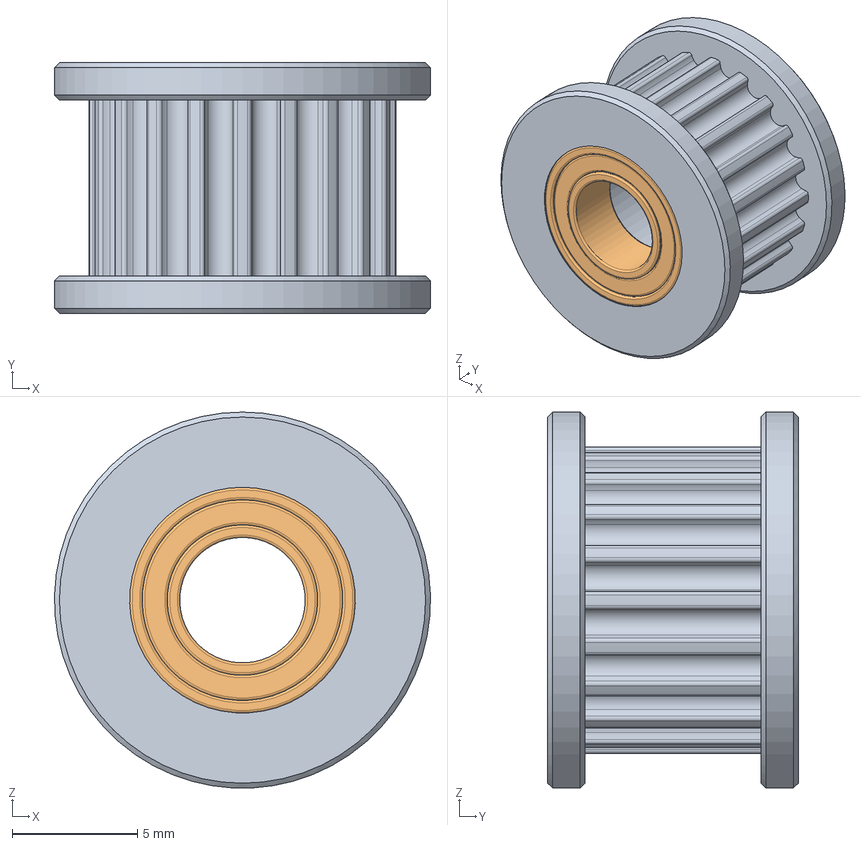
[picture p61: CAD file, 2025-05-13]
Design_Files/Alice - Claw_Machine_V3/7_3 Cube Parts/Sub_Assemblys/2020-extrusion-gt2-belt-tensioner/GT2_Idler_20T_6mm.step
15.0 x 10.0 x 15.0 mm
GT2_Idler_20T
Ball bearing (5x9x3)mm003
Ball bearing (5x9x3)mm004
