cheshire-smile/CSULA_ECST_Claw_Machine/Design_Files/Alice - Claw_Machine_V3/7_3 Cube Parts/Winch/Middle part 5mm.SLDPRT

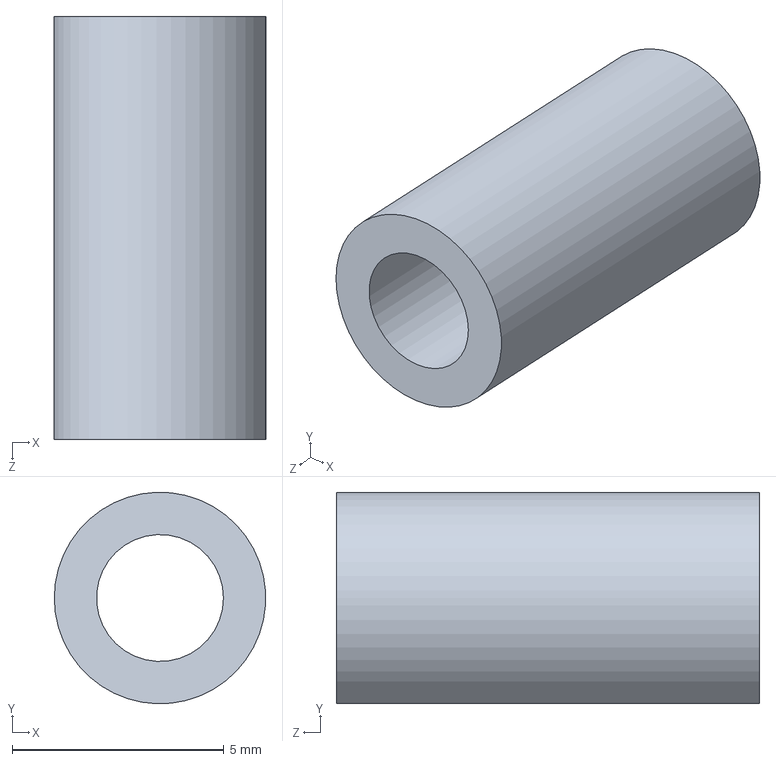
[picture p62: CAD file, 2025-05-13]
Design_Files/Alice - Claw_Machine_V3/7_3 Cube Parts/Winch/Middle part 5mm.SLDPRT
5.00 x 5.00 x 10.0 mm
