cheshire-smile/CSULA_ECST_Claw_Machine/Design_Files/Alice - Claw_Machine_V3/7_3 Cube Parts/X-Axis_Mounting_Bracket.SLDPRT

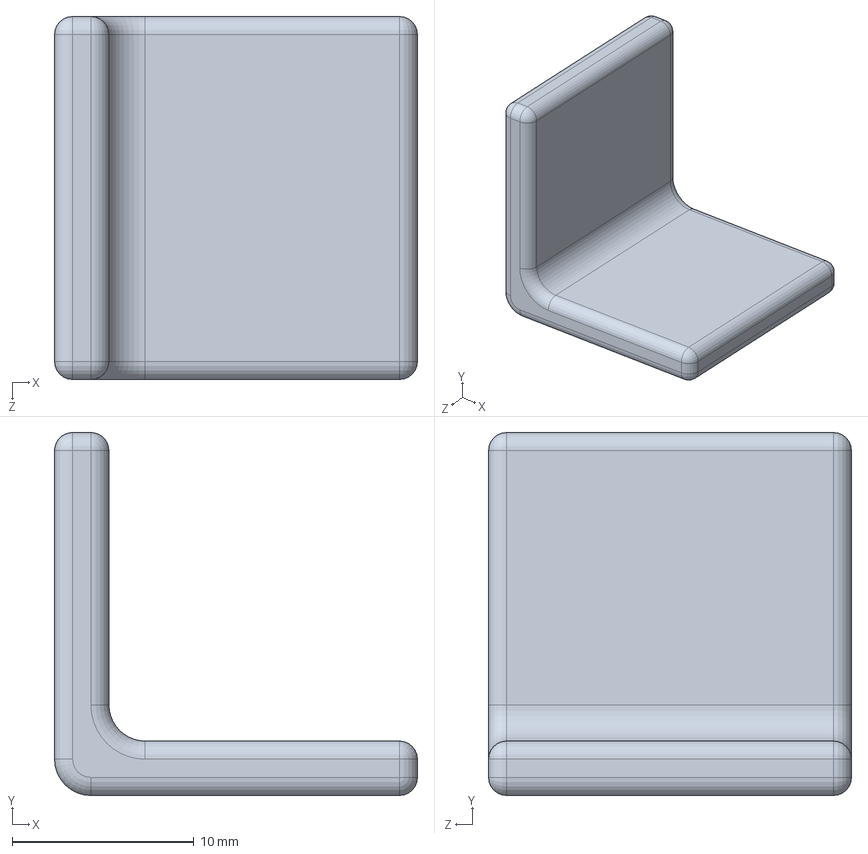
[picture p63: CAD file, 2025-05-13]
Design_Files/Alice - Claw_Machine_V3/7_3 Cube Parts/X-Axis_Mounting_Bracket.SLDPRT
20.0 x 20.0 x 20.0 mm
