cheshire-smile/CSULA_ECST_Claw_Machine/Design_Files/Claw_Machine_V5/7_3 Cube Parts/Ke goc 28x28x20mm.SLDPRT

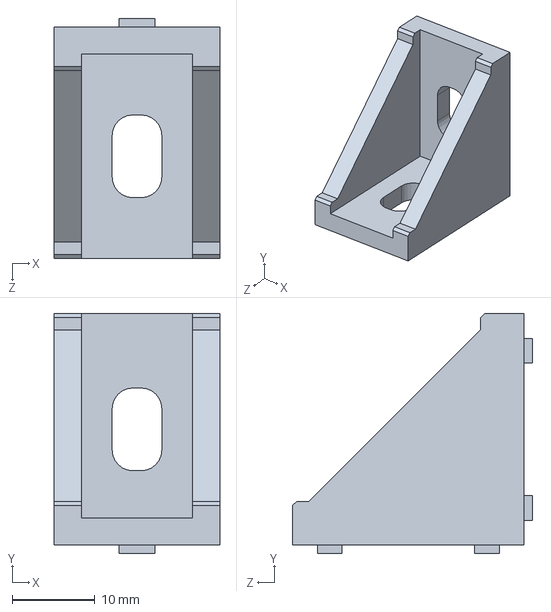
[picture p64: CAD file, 2025-09-01]
Design_Files/Claw_Machine_V5/7_3 Cube Parts/Ke goc 28x28x20mm.SLDPRT
20.0 x 29.0 x 29.0 mm
