cheshire-smile/CSULA_ECST_Claw_Machine/Design_Files/Claw_Machine_V5/7_3 Cube Parts/Sub_Assemblys/Mini Servo operated Claw Machine Claw Grabber - 4826548/files/Servo_Linkage_Part_2.SLDPRT

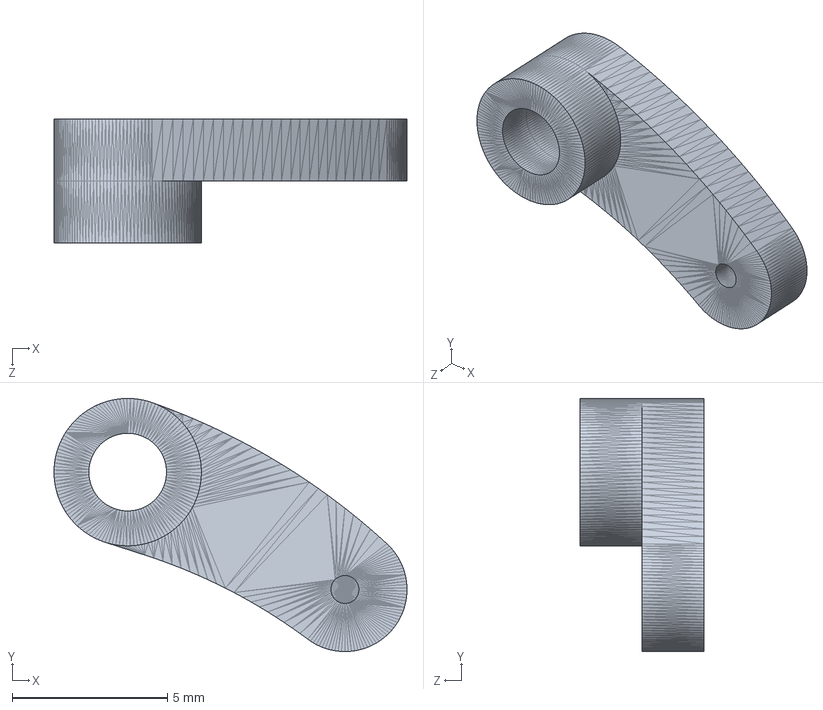
[picture p65: CAD file, 2025-05-13]
Design_Files/Claw_Machine_V5/7_3 Cube Parts/Sub_Assemblys/Mini Servo operated Claw Machine Claw Grabber - 4826548/files/Servo_Linkage_Part_2.SLDPRT
11.4 x 8.16 x 4.00 mm
