cheshire-smile/CSULA_ECST_Claw_Machine/Design_Files/Alice - Claw_Machine_V3/7_3 Cube Parts/wood/23.92inx160.37mmwoodforjoystick.SLDPRT

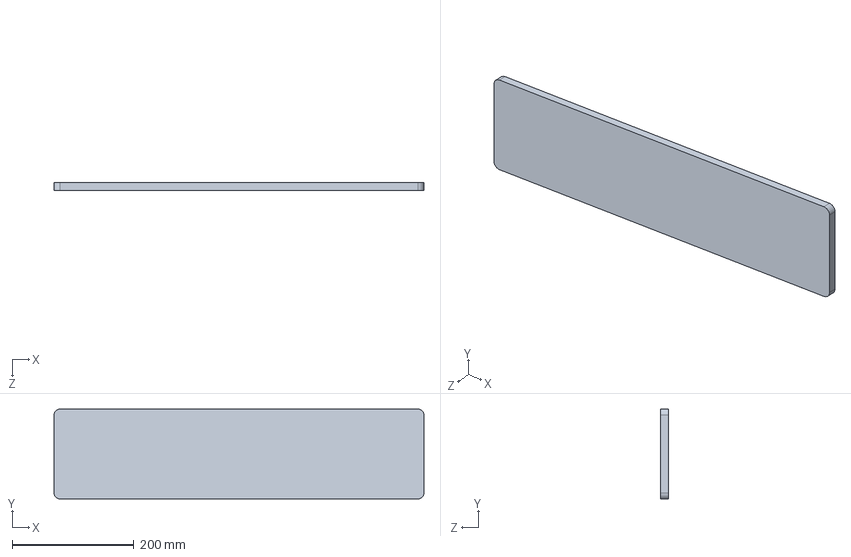
[picture p66: CAD file, 2025-05-13]
Design_Files/Alice - Claw_Machine_V3/7_3 Cube Parts/wood/23.92inx160.37mmwoodforjoystick.SLDPRT
607.6 x 147.7 x 12.7 mm
