cheshire-smile/CSULA_ECST_Claw_Machine/Design_Files/Alice - Claw_Machine_V3/7_3 Cube Parts/Corner_Idler_Pulley.SLDPRT

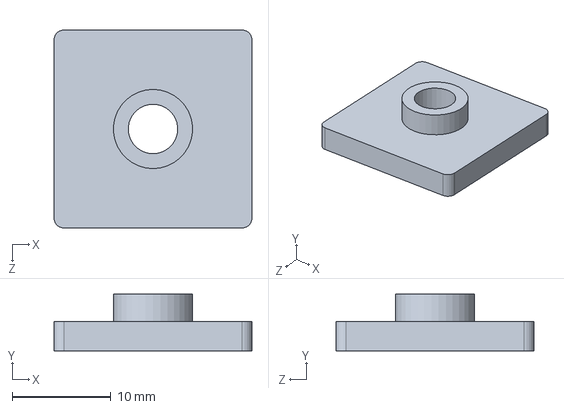
[picture p67: CAD file, 2025-05-13]
Design_Files/Alice - Claw_Machine_V3/7_3 Cube Parts/Corner_Idler_Pulley.SLDPRT
20.0 x 5.75 x 20.0 mm
