cheshire-smile/CSULA_ECST_Claw_Machine/Design_Files/Alice - Claw_Machine_V3/7_3 Cube Parts/Winch/Combined part.SLDASM

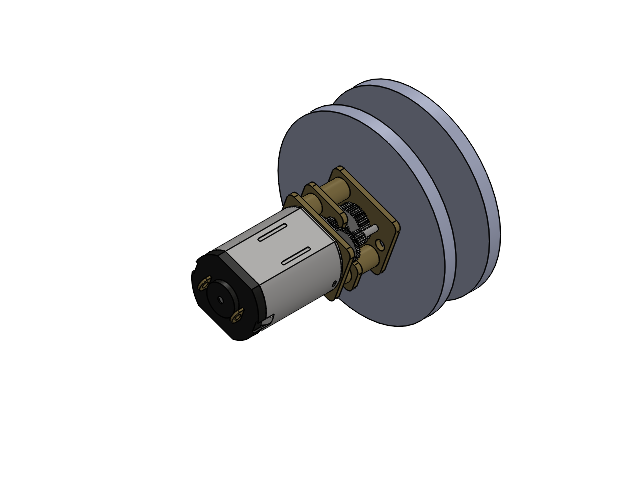
[picture p76: CAD file, 2025-05-13]
Design_Files/Alice - Claw_Machine_V3/7_3 Cube Parts/Winch/Combined part.SLDASM
Updated Spool
Engrenagem reta1.stp
Engrenagem reta2.stp
Engrenagem reta1_1.stp
Engrenagem reta2_1.stp
Engrenagem reta1_2.stp
Engrenagem reta2_2.stp
Engrenagem reta1_3.stp
Engrenagem reta2_3.stp
Engrenagem reta1_4.stp
Engrenagem reta2_4.stp
Base.stp
Rotor.stp
Apoio Contato.stp
Contato.stp
Suporte Contato.stp
Im_X_E3s.stp
Terminais.stp x 2
Escovas.stp
Chapa Inferior.stp
Chapa Intermedi_X_E1ria.stp
Chapa Superior.stp
Eixo Maior - Engrenagem.stp
Eixo Menor - Engrenagem.stp
Parafuso.stp x 2
Suporte Bobinas.stp
Eixo Menor - Engrenagem_1.stp
Eixo - Encaixe D.stp
Carca_X_E7a.stp
