cheshire-smile/CSULA_ECST_Claw_Machine/Design_Files/Alice - Claw_Machine_V3/7_3 Cube Parts/Sub_Assemblys/dc-micro-metal-gearmotor/GearMotor/Motor.png

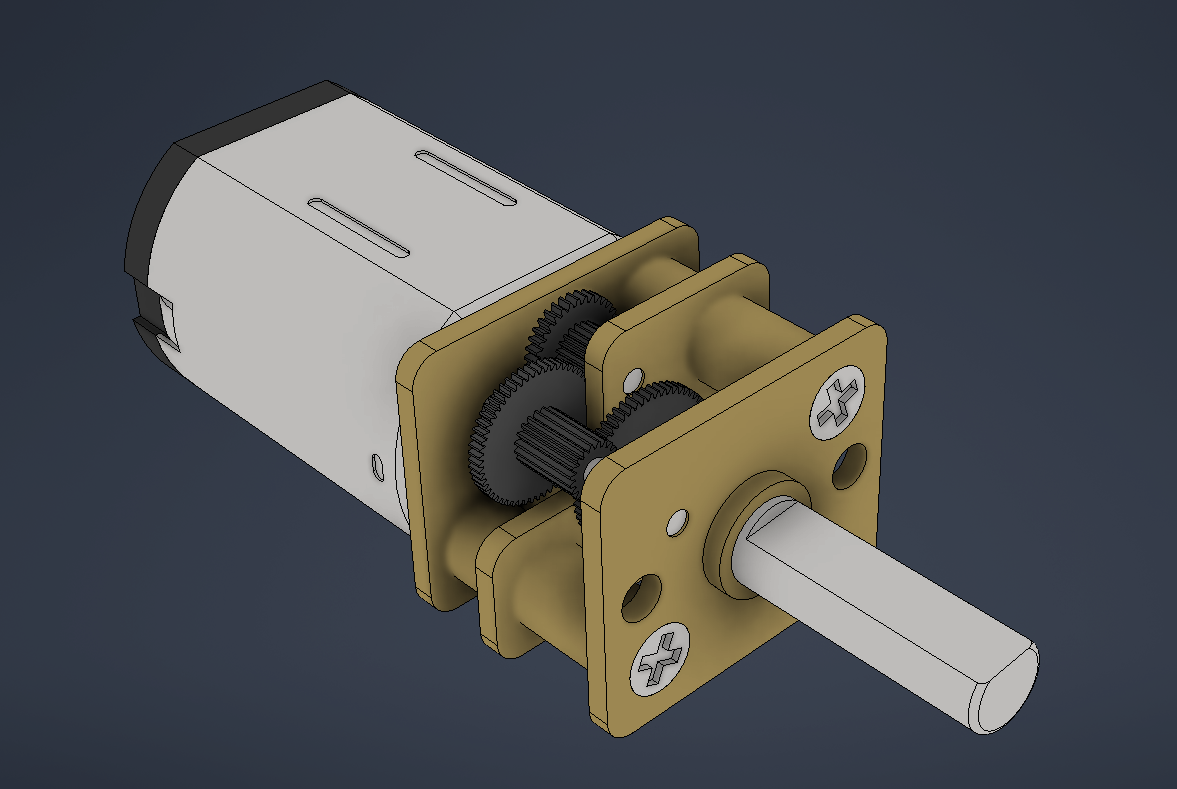
Design_Files/Alice - Claw_Machine_V3/7_3 Cube Parts/Sub_Assemblys/dc-micro-metal-gearmotor/GearMotor/Motor.png
